next-hack/uSVC/images/32spritedemo.png

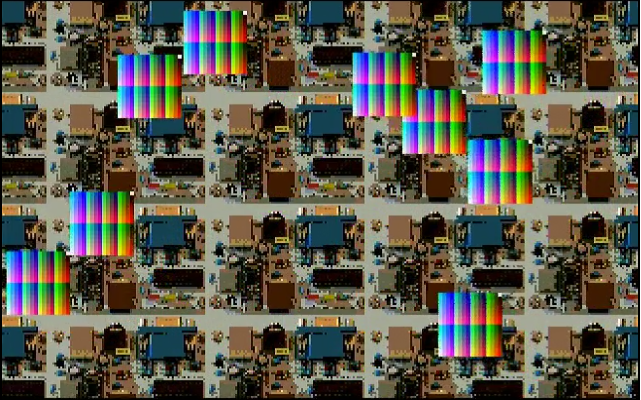
images/32spritedemo.png
