next-hack/uSVC/images/gameLoader.png

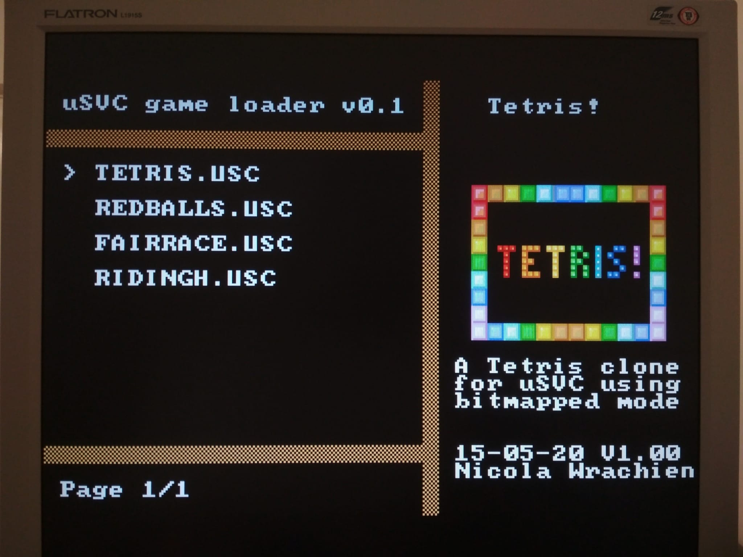
images/gameLoader.png
