next-hack/uSVC/images/redballs1.png

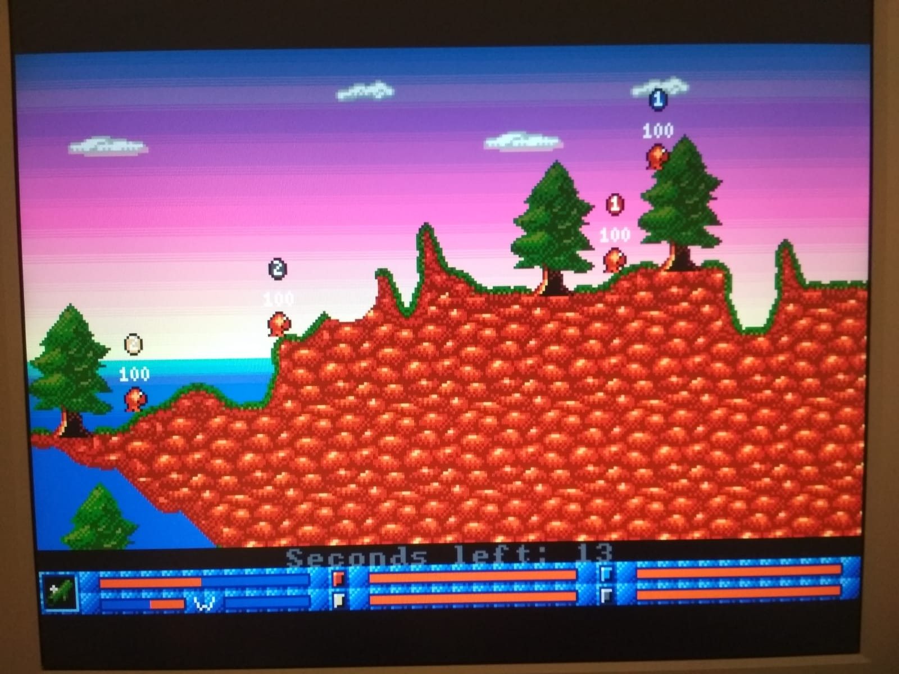
images/redballs1.png
