next-hack/uSVC/images/redballs2.png

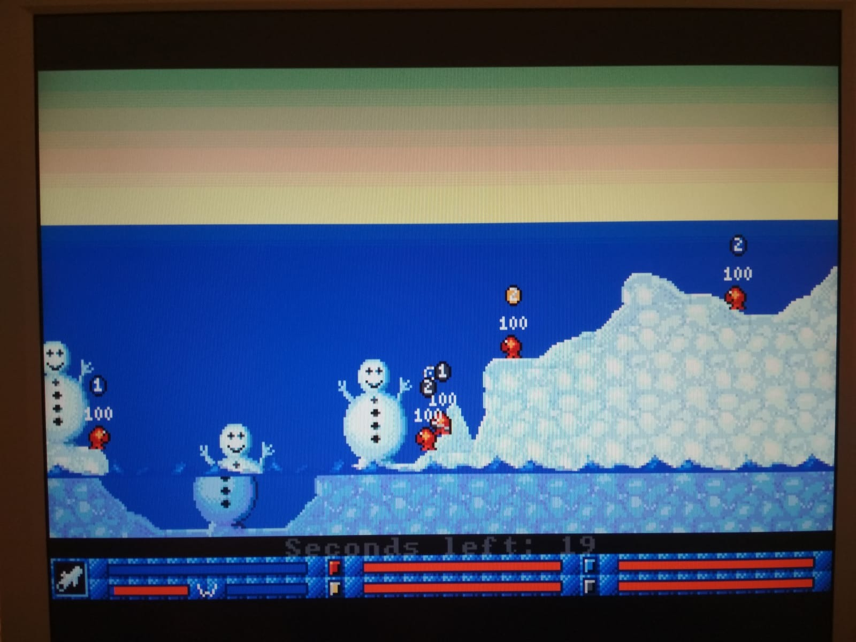
images/redballs2.png
