next-hack/uSVC/images/riding horse.png

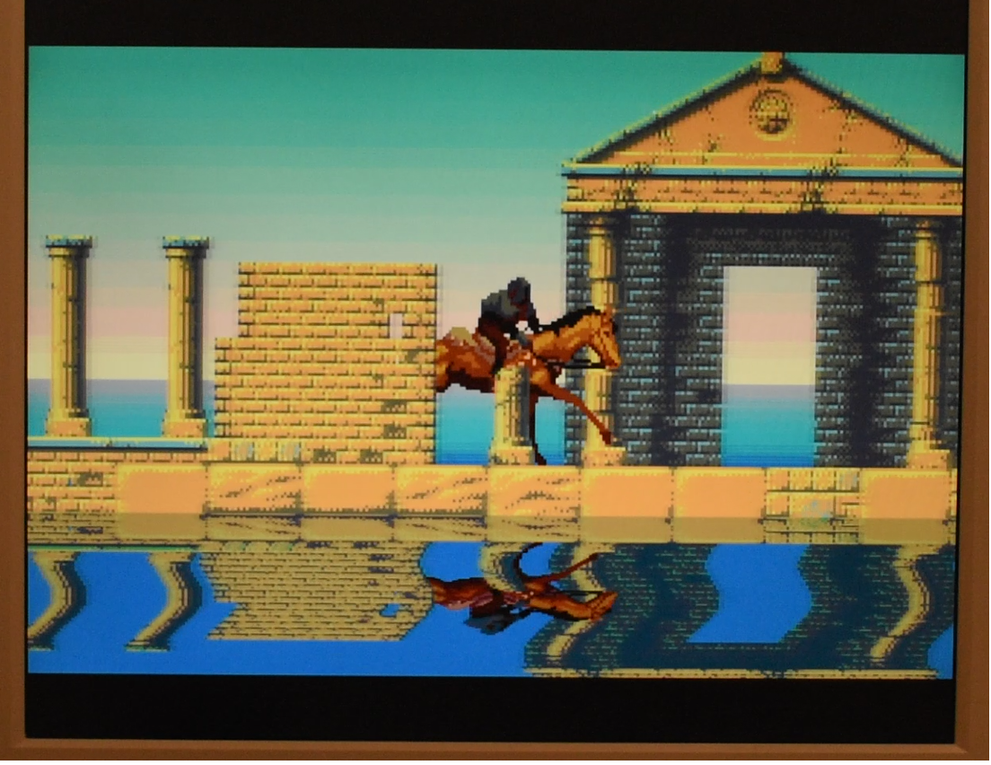
images/riding horse.png
