next-hack/uSVC/images/sprites8x8.png

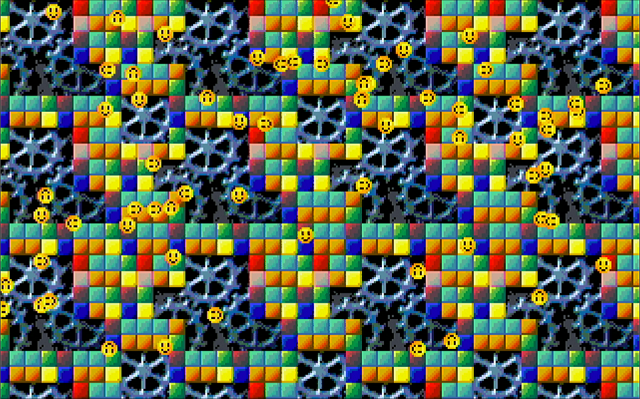
images/sprites8x8.png
