next-hack/uSVC/images/usvc connected.jpg

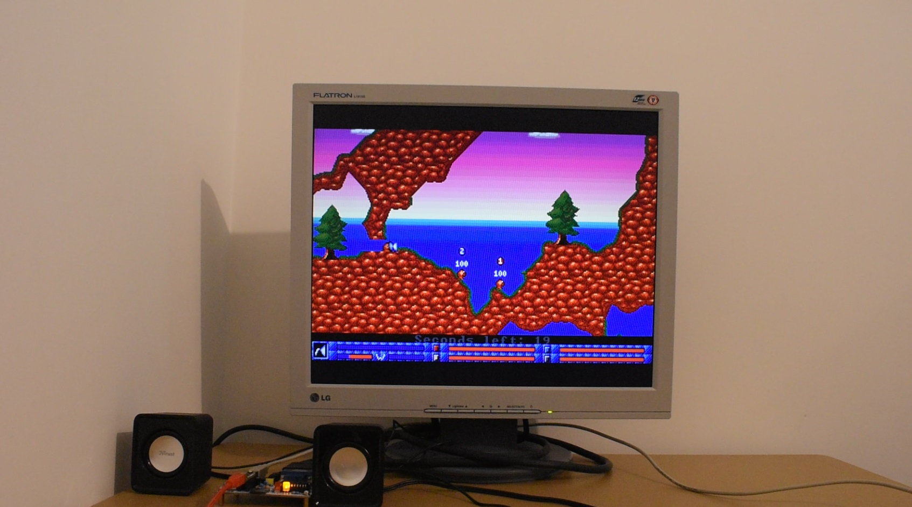
images/usvc connected.jpg
