next-hack/uSVC/images/usvc fits in your hand-red.jpg

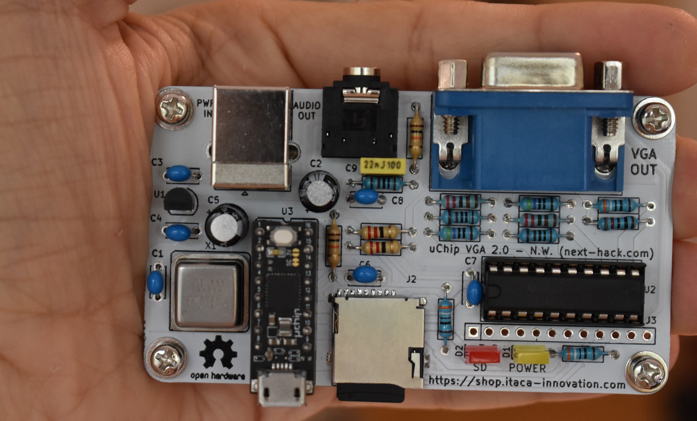
images/usvc fits in your hand-red.jpg
