next-hack/uSVC/images/usvcEditor.png

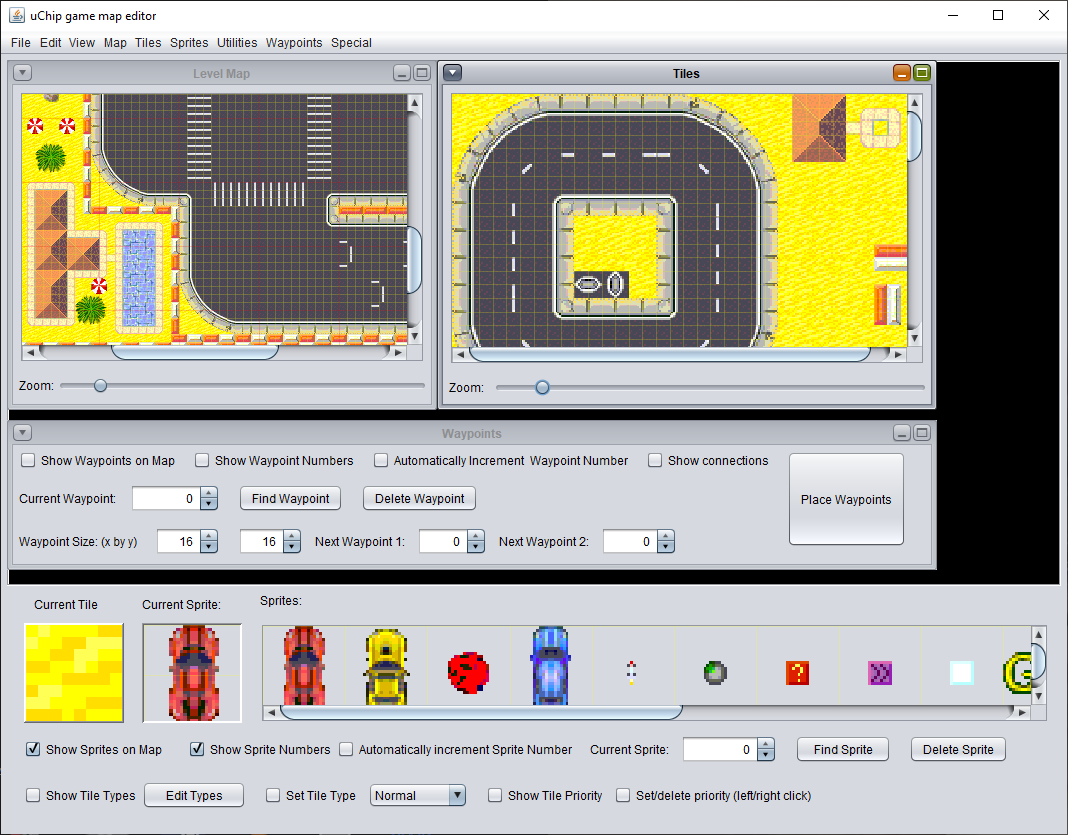
images/usvcEditor.png
