next-hack/uSVC/software/uSVC_GameLoader/soundData.c

/*
 *  RedBalls (not in the UrbanDictionary definintion!): 
 *  A clone of the popular Worms game, runnin on uChip Simple VGA Console
 *  a simple Cortex M0+ console with 32 kB of RAM!
 *
 *  Copyright 2019-2020 Nicola Wrachien (next-hack.com)
 *
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
 *  tl;dr 
 *  Do whatever you want, this program is free! Though we won't 
 *  reject donations https://next-hack.com/index.php/donate/ :) 
 *
 *
 * soundData.h/c: these files defines the actual PCM samples. 
 * I used  WAVToCode (Copyright (C) 2018-2020 C. J. Seymour)
 * to create the arrays. 
 */
#include "soundData.h" 
/**********************************************************************
* Written by WAVToCode
* Date:				Thu Apr 02 09:02:51 AM
* FileName:			ak47.c
* Interleaved:		N/A
* Signed:			Yes
* No. of channels:	1
* No. of samples:	1268
* Bits/Sample:		8
* Sps: 30k
**********************************************************************/

const char ak47_data[AK47_NUM_ELEMENTS] = {
	0,   0,   0,   0,   0,   0,   0,   0, /* 0-7 */
	0,   0,   0,   0,   0,   0,   0,   0, /* 8-15 */
	0,   0,   0,   0,   0,   0,   0,   0, /* 16-23 */
	0,   0,   0,   0,   0,   0,   0,   0, /* 24-31 */
	0,   0,   0,   0,   0,   0,   0,   0, /* 32-39 */
	0,   0,   0,   0,   0,   0,   0,   0, /* 40-47 */
	0,   0,   0,   0,   0,   0,   0,   0, /* 48-55 */
	0,   0,   0,   0,   0,   0,   0,   0, /* 56-63 */
	0,   0,   0,   0,   0,   0,   0,   0, /* 64-71 */
	-1,   0,  -2,  -6, -12,  16,  42,  33, /* 72-79 */
	28,  18,  17,  15,   2,  -6, -13, -17, /* 80-87 */
	-15, -14, -16, -14, -12, -11, -11, -11, /* 88-95 */
	-9,  -7,  -8,  -6,  -3,  -1,   0,   0, /* 96-103 */
	0,   1,  -1,  -2,   3,   2,   1,  -1, /* 104-111 */
	0,   2,  -1,   3,   0,   0,   2,   0, /* 112-119 */
	2,   0,   1,   1,   1,   0,  -1,   1, /* 120-127 */
	0,  -1,  -2,  -1,   0,   0,  -1,   1, /* 128-135 */
	1,   0,  -1,  -2,   1,   3,   0,  -3, /* 136-143 */
	-2,  -1,   0,   0,  -1,  -1,   0,  -1, /* 144-151 */
	-1,   0,  -1,  -1,   0,  -1,  -1,  -1, /* 152-159 */
	0,   0,   0,   0,  -1,  -1,   0,   0, /* 160-167 */
	0,  -1,  -1,   0,   0,   0,   0,  -1, /* 168-175 */
	0,   0,   0,   0,   0,   0,  -1,   0, /* 176-183 */
	-2,  -1,   0,   0,   0,  -1,  -1,   0, /* 184-191 */
	0,  -1,  -2,  -1,   0,  -1,   0,  -1, /* 192-199 */
	0,  -2,  -1,   0,  -1,   0,  -1,   0, /* 200-207 */
	-1,  -1,   0,   0,   1,  -1,  -1,   0, /* 208-215 */
	-1,  -1,  -1,   0,  -1,  -1,   0,   0, /* 216-223 */
	0,  -1,  -1,  -1,  -1,   0,  -1,  -1, /* 224-231 */
	-1,  -1,   0,  -1,  -1,  -1,  -1,  -1, /* 232-239 */
	0,   0,   0,  -1,  -1,  -1,   0,  -1, /* 240-247 */
	-1,  -1,  -1,   0,  -1,  -1,  -1,   0, /* 248-255 */
	-1,  -1,   0,   0,  -1,  -1,  -1,   0, /* 256-263 */
	0,   0,  -1,   0,  -1,  -1,  -1,  -1, /* 264-271 */
	0,  -1,   0,  -1,   0,  -1,   0,  -1, /* 272-279 */
	-1,  -2,  -1,   0,   0,  -2,  -1,  -1, /* 280-287 */
	0,   0,   0,  -1,  -1,   1,  -1,   0, /* 288-295 */
	-1,   0,  -2,   1,  -2,   2,  -3,   4, /* 296-303 */
	-4,   7, -28, -56, -62, -57,  35,  65, /* 304-311 */
	117, 127, 124,  63,  -4, -18, -53, -67, /* 312-319 */
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
	
