next-hack/uSVC/software/uSVC_GameLoader/usvc_kernel/defaultSounds.c

/*
*  Default UzeBox sounds, copyright Alec Bourque (Belogic Software, UzeBox project).
*  
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
*  You should have received a copy of the GNU General Public License
*  along with this program.  If not, see <http://www.gnu.org/licenses/>. 
*/
#include <stdint.h> 
#include "defaultSounds.h"
#if INCLUDE_DEFAULT_WAVES
const int8_t sineWave[] =
{
	0x00,0x03,0x06,0x09,0x0C,0x10,0x13,0x16,0x19,0x1C,0x1F,0x22,0x25,0x28,0x2B,0x2E,
	0x31,0x33,0x36,0x39,0x3C,0x3F,0x41,0x44,0x47,0x49,0x4C,0x4E,0x51,0x53,0x55,0x58,
	0x5A,0x5C,0x5E,0x60,0x62,0x64,0x66,0x68,0x6A,0x6B,0x6D,0x6F,0x70,0x71,0x73,0x74,
	0x75,0x76,0x78,0x79,0x7A,0x7A,0x7B,0x7C,0x7D,0x7D,0x7E,0x7E,0x7E,0x7F,0x7F,0x7F,
	0x7F,0x7F,0x7F,0x7F,0x7E,0x7E,0x7E,0x7D,0x7D,0x7C,0x7B,0x7A,0x7A,0x79,0x78,0x76,
	0x75,0x74,0x73,0x71,0x70,0x6F,0x6D,0x6B,0x6A,0x68,0x66,0x64,0x62,0x60,0x5E,0x5C,
	0x5A,0x58,0x55,0x53,0x51,0x4E,0x4C,0x49,0x47,0x44,0x41,0x3F,0x3C,0x39,0x36,0x33,
	0x31,0x2E,0x2B,0x28,0x25,0x22,0x1F,0x1C,0x19,0x16,0x13,0x10,0x0C,0x09,0x06,0x03,
	0x00,0xFD,0xFA,0xF7,0xF4,0xF0,0xED,0xEA,0xE7,0xE4,0xE1,0xDE,0xDB,0xD8,0xD5,0xD2,
	0xCF,0xCD,0xCA,0xC7,0xC4,0xC1,0xBF,0xBC,0xB9,0xB7,0xB4,0xB2,0xAF,0xAD,0xAB,0xA8,
	0xA6,0xA4,0xA2,0xA0,0x9E,0x9C,0x9A,0x98,0x96,0x95,0x93,0x91,0x90,0x8F,0x8D,0x8C,
	0x8B,0x8A,0x88,0x87,0x86,0x86,0x85,0x84,0x83,0x83,0x82,0x82,0x82,0x81,0x81,0x81,
	0x81,0x81,0x81,0x81,0x82,0x82,0x82,0x83,0x83,0x84,0x85,0x86,0x86,0x87,0x88,0x8A,
	0x8B,0x8C,0x8D,0x8F,0x90,0x91,0x93,0x95,0x96,0x98,0x9A,0x9C,0x9E,0xA0,0xA2,0xA4,
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
	,0x80,0x80,0x80,0x80,0x80,0x80,0x80,0x80,0x80,0x80,0x80,0x80,0x80,0x80,0x80,0x80
	,0x80,0x80,0x80,0x80,0x80,0x80,0x80,0x80,0x80,0x80,0x80,0x80,0x80,0x80,0x80,0x80
	,0x80,0x80,0x80,0x80,0x80,0x87,0x91,0x9d,0xac,0xc4,0xcb,0xd4,0xdd,0xf2,0xfa,0xfa	
};

#endif
