next-hack/uSVC/software/uSVC_GameLoader/usvc_kernel/stepTable.c

/*
*  uChip Simple VGA Console Kernel, a minimalistic console with VGA and USB support using uChip!
*
*  Copyright 2019-2020 Nicola Wrachien (next-hack.com)
*
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
*  tl;dr
*  Do whatever you want, this program is free! Though we won't
*  reject donations https://next-hack.com/index.php/donate/ :)
*
*  stepTable.c. Since the sampling frequency is fixed at 30kHz, and the
*  default sounds have 256 samples, for each note we need an increment
*  for decimation/integration.
*/
#include <stdint.h> 
const uint16_t stepTable[128] =
{
	0x0012, // Note 0 (C-1), frequency 8.175799, Step 0.070313
	0x0013, // Note 1 (C#-1), frequency 8.661957, Step 0.074219
	0x0014, // Note 2 (D-1), frequency 9.177024, Step 0.078125
	0x0015, // Note 3 (D#-1), frequency 9.722718, Step 0.082031
	0x0017, // Note 4 (E-1), frequency 10.300861, Step 0.089844
	0x0018, // Note 5 (F-1), frequency 10.913382, Step 0.093750
	0x0019, // Note 6 (F#-1), frequency 11.562326, Step 0.097656
	0x001B, // Note 7 (G-1), frequency 12.249857, Step 0.105469
	0x001C, // Note 8 (G#-1), frequency 12.978272, Step 0.109375
	0x001E, // Note 9 (A-1), frequency 13.750000, Step 0.117188
	0x0020, // Note 10 (A#-1), frequency 14.567618, Step 0.125000
	0x0022, // Note 11 (B-1), frequency 15.433853, Step 0.132813
	0x0024, // Note 12 (C-2), frequency 16.351598, Step 0.140625
	0x0026, // Note 13 (C#-2), frequency 17.323914, Step 0.148438
	0x0028, // Note 14 (D-2), frequency 18.354048, Step 0.156250
	0x002A, // Note 15 (D#-2), frequency 19.445436, Step 0.164063
	0x002D, // Note 16 (E-2), frequency 20.601722, Step 0.175781
	0x0030, // Note 17 (F-2), frequency 21.826764, Step 0.187500
	0x0033, // Note 18 (F#-2), frequency 23.124651, Step 0.199219
	0x0036, // Note 19 (G-2), frequency 24.499715, Step 0.210938
	0x0039, // Note 20 (G#-2), frequency 25.956544, Step 0.222656
	0x003C, // Note 21 (A-2), frequency 27.500000, Step 0.234375
	0x0040, // Note 22 (A#-2), frequency 29.135235, Step 0.250000
	0x0043, // Note 23 (B-2), frequency 30.867706, Step 0.261719
	0x0047, // Note 24 (C-3), frequency 32.703196, Step 0.277344
	0x004C, // Note 25 (C#-3), frequency 34.647829, Step 0.296875
	0x0050, // Note 26 (D-3), frequency 36.708096, Step 0.312500
	0x0055, // Note 27 (D#-3), frequency 38.890873, Step 0.332031
	0x005A, // Note 28 (E-3), frequency 41.203445, Step 0.351563
	0x005F, // Note 29 (F-3), frequency 43.653529, Step 0.371094
	0x0065, // Note 30 (F#-3), frequency 46.249303, Step 0.394531
	0x006B, // Note 31 (G-3), frequency 48.999429, Step 0.417969
	0x0071, // Note 32 (G#-3), frequency 51.913087, Step 0.441406
	0x0078, // Note 33 (A-3), frequency 55.000000, Step 0.468750
	0x007F, // Note 34 (A#-3), frequency 58.270470, Step 0.496094
	0x0087, // Note 35 (B-3), frequency 61.735413, Step 0.527344
	0x008F, // Note 36 (C-4), frequency 65.406391, Step 0.558594
	0x0097, // Note 37 (C#-4), frequency 69.295658, Step 0.589844
	0x00A0, // Note 38 (D-4), frequency 73.416192, Step 0.625000
	0x00AA, // Note 39 (D#-4), frequency 77.781746, Step 0.664063
	0x00B4, // Note 40 (E-4), frequency 82.406889, Step 0.703125
	0x00BF, // Note 41 (F-4), frequency 87.307058, Step 0.746094
	0x00CA, // Note 42 (F#-4), frequency 92.498606, Step 0.789063
	0x00D6, // Note 43 (G-4), frequency 97.998859, Step 0.835938
	0x00E3, // Note 44 (G#-4), frequency 103.826174, Step 0.886719
	0x00F0, // Note 45 (A-4), frequency 110.000000, Step 0.937500
	0x00FF, // Note 46 (A#-4), frequency 116.540940, Step 0.996094
	0x010E, // Note 47 (B-4), frequency 123.470825, Step 1.054688
	0x011E, // Note 48 (C-5), frequency 130.812783, Step 1.117188
	0x012F, // Note 49 (C#-5), frequency 138.591315, Step 1.183594
	0x0141, // Note 50 (D-5), frequency 146.832384, Step 1.253906
	0x0154, // Note 51 (D#-5), frequency 155.563492, Step 1.328125
	0x0168, // Note 52 (E-5), frequency 164.813778, Step 1.406250
	0x017D, // Note 53 (F-5), frequency 174.614116, Step 1.488281
	0x0194, // Note 54 (F#-5), frequency 184.997211, Step 1.578125
	0x01AC, // Note 55 (G-5), frequency 195.997718, Step 1.671875
	0x01C6, // Note 56 (G#-5), frequency 207.652349, Step 1.773438
	0x01E1, // Note 57 (A-5), frequency 220.000000, Step 1.878906
	0x01FD, // Note 58 (A#-5), frequency 233.081881, Step 1.988281
	0x021B, // Note 59 (B-5), frequency 246.941651, Step 2.105469
	0x023C, // Note 60 (C-6), frequency 261.625565, Step 2.234375
	0x025E, // Note 61 (C#-6), frequency 277.182631, Step 2.367188
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
	0x5A03, // Note 124 (E-11), frequency 10548.081821, Step 90.011719
	0x5F5D, // Note 125 (F-11), frequency 11175.303406, Step 95.363281
	0x6508, // Note 126 (F#-11), frequency 11839.821527, Step 101.031250
	0x6B0A // Note 127 (G-11), frequency 12543.853951, Step 107.039063
};
