next-hack/uSVC/software/uSVC_GameLoader/logoTiles.c

/*	USVC Game Loader and libraries
*
 *  Copyright 2019-2020 Nicola Wrachien (next-hack.com)
 *
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
 *  tl;dr 
 *  Do whatever you want, this program is free! Though we won't 
 *  reject donations https://next-hack.com/index.php/donate/ :) 
 *
 */
#include "logoTiles.h"
#include "usvc_kernel/vgaConstants.h"
const uint8_t tilePalette[] = 
{0x00 , 0x56, 0x97, 0xD7, 
0x00 , COLOR_TORGB332(7, 4, 0), COLOR_TORGB332(7, 7, 0), COLOR_TORGB332(7, 7, 2),
0x00 , COLOR_TORGB332(7, 5, 1), COLOR_TORGB332(7, 7, 1), COLOR_TORGB332(7, 7, 3),
0x00 , COLOR_TORGB332(7, 6, 2), COLOR_TORGB332(7, 7, 2), COLOR_TORGB332(7, 7, 3),
0x00 , COLOR_TORGB332(7, 6, 3), COLOR_TORGB332(7, 7, 3), COLOR_TORGB332(7, 7, 3),
0x00 , COLOR_TORGB332(7, 6, 2), COLOR_TORGB332(7, 7, 2), COLOR_TORGB332(7, 7, 3),
0x00 , COLOR_TORGB332(7, 5, 1), COLOR_TORGB332(7, 7, 1), COLOR_TORGB332(7, 7, 3),
0x00 , COLOR_TORGB332(7, 4, 0), COLOR_TORGB332(7, 7, 0), COLOR_TORGB332(7, 7, 2),
0x00, COLOR_TORGB332(6, 3, 0), COLOR_TORGB332(7, 5, 0), COLOR_TORGB332(7, 7, 0),
0x00, COLOR_TORGB332(4, 2, 0), COLOR_TORGB332(5, 3, 0), COLOR_TORGB332(5, 4, 0),
0x00, COLOR_TORGB332(2, 1, 0), COLOR_TORGB332(3, 2, 0), COLOR_TORGB332(3, 3, 0),
0x00, COLOR_TORGB332(1, 0, 0), COLOR_TORGB332(2, 1, 0), COLOR_TORGB332(2, 2, 0),
0x00, COLOR_TORGB332(0, 0, 0), COLOR_TORGB332(1, 0, 0), COLOR_TORGB332(1, 1, 0),
0x00, 0, 0, 0,
}; // the second part is the highlighted one

const uint8_t tileData[MAXTILEINDEX][TILESIZEX * TILESIZEY / 4 ] =
{
// 	{  first tile is black. We wont' save it!
// 		0x00, 0x00, 0x00, 0x00, 0x00, 0x00, 0x00, 0x00, 0x00, 0x00, 0x00, 0x00, 0x00, 0x00, 0x00, 0x00
// 	},
	{
		0x00, 0x40, 0x00, 0x90, 0x00, 0xE4, 0x00, 0xF9, 0x40, 0xFE, 0x90, 0xFF, 0xE4, 0xFF, 0xF9, 0xFF
	},
	{
		0x55, 0x55, 0xAA, 0xAA, 0xFF, 0xFF, 0xFF, 0xFF, 0xFF, 0xFF, 0xFF, 0xFF, 0xFF, 0xFF, 0xFF, 0xFF
	},
	{
		0x01, 0x00, 0x06, 0x00, 0x1B, 0x00, 0x6F, 0x00, 0xBF, 0x01, 0xFF, 0x06, 0xFF, 0x1B, 0xFF, 0x6F
	},
	{
		0xFF, 0xFF, 0xFF, 0xFF, 0xFF, 0xFF, 0xFF, 0xFF, 0xFF, 0xFF, 0xFF, 0xFF, 0xFF, 0xFF, 0xFF, 0xBF
	},
	{
		0xFF, 0xFF, 0xFF, 0xFF, 0xFF, 0xFF, 0xFF, 0xFF, 0xFF, 0xFF, 0xFF, 0xFF, 0xFF, 0xFF, 0xFE, 0xFF
	},
	{
		0xF9, 0xFF, 0xF9, 0xFF, 0xF9, 0xFF, 0xF9, 0xFF, 0xF9, 0xFF, 0xF9, 0xFF, 0xF9, 0xFF, 0xF9, 0xFF
	},
	{
		0xFF, 0xFF, 0xFF, 0xFF, 0xFF, 0xFF, 0xFF, 0xFF, 0xFF, 0xFF, 0xFF, 0xFF, 0xFF, 0xFF, 0xFF, 0xFF
	},
	{
		0xFF, 0x6F, 0xFF, 0x6F, 0xFF, 0x6F, 0xFF, 0x6F, 0xFF, 0x6F, 0xFF, 0x6F, 0xFF, 0x6F, 0xFF, 0x6F
	},
	{
		0xFF, 0xBF, 0xFF, 0xFF, 0xFF, 0xFF, 0xFF, 0xFF, 0xFF, 0xFF, 0xFF, 0xFF, 0xFF, 0xFF, 0xFF, 0xFF
	},
	{
		0xFE, 0xFF, 0xFF, 0xFF, 0xFF, 0xFF, 0xFF, 0xFF, 0xFF, 0xFF, 0xFF, 0xFF, 0xFF, 0xFF, 0xFF, 0xFF
	},
	{
		0xF9, 0xFF, 0xE4, 0xFF, 0x90, 0xFF, 0x40, 0xFE, 0x00, 0xF9, 0x00, 0xE4, 0x00, 0x90, 0x00, 0x40
	},
	{
		0xFF, 0xFF, 0xFF, 0xFF, 0xFF, 0xFF, 0xFF, 0xFF, 0xFF, 0xFF, 0xFF, 0xFF, 0xAA, 0xAA, 0x55, 0x55
	},
	{
		0xFF, 0x6F, 0xFF, 0x1B, 0xFF, 0x06, 0xBF, 0x01, 0x6F, 0x00, 0x1B, 0x00, 0x06, 0x00, 0x01, 0x00
	}
};
