next-hack/uSVC/software/uSVC_GameLoader/usvcLogoMap.c

/*	USVC Game Loader and libraries
*
 *  Copyright 2019-2020 Nicola Wrachien (next-hack.com)
 *
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
 *  tl;dr 
 *  Do whatever you want, this program is free! Though we won't 
 *  reject donations https://next-hack.com/index.php/donate/ :) 
 *
 */
#include "usvcLogoMap.h"
#define NIBBLES2B(a,b) (a | (b << 4))
#define ROWOFNIBBLES2BYTES(a0, a1, a2, a3, a4, a5, a6, a7)  NIBBLES2B(a0,a1),NIBBLES2B(a2,a3),NIBBLES2B(a4,a5),NIBBLES2B(a6,a7)
const uint8_t logoMap[MAPSIZEY_LOGO * MAPSIZEX_LOGO/2] =
{
	ROWOFNIBBLES2BYTES(0x0000, 0x0000, 0x0000, 0x0000, 0x0000, 0x0000, 0x0000, 0x0000),
	ROWOFNIBBLES2BYTES(0x0000, 0x0001, 0x0002, 0x0002, 0x0002, 0x0002, 0x0002, 0x0003),
	ROWOFNIBBLES2BYTES(0x0000, 0x0001, 0x0003, 0x0000, 0x0000, 0x0000, 0x0000, 0x0001),
	ROWOFNIBBLES2BYTES(0x0003, 0x0000, 0x0000, 0x0001, 0x0002, 0x0002, 0x0002, 0x0002),
	ROWOFNIBBLES2BYTES(0x0002, 0x0003, 0x0000, 0x0000, 0x0000, 0x0000, 0x0000, 0x0000),
	ROWOFNIBBLES2BYTES(0x0000, 0x0000, 0x0001, 0x000A, 0x0004, 0x000C, 0x000C, 0x000C),
	ROWOFNIBBLES2BYTES(0x000C, 0x000D, 0x0000, 0x0006, 0x0008, 0x0000, 0x0000, 0x0000),
	ROWOFNIBBLES2BYTES(0x0000, 0x0006, 0x0008, 0x0000, 0x0001, 0x000A, 0x0004, 0x000C),
	ROWOFNIBBLES2BYTES(0x000C, 0x000C, 0x000C, 0x000D, 0x0000, 0x0000, 0x0000, 0x0000),
	ROWOFNIBBLES2BYTES(0x0000, 0x0000, 0x0000, 0x0000, 0x0006, 0x0004, 0x000D, 0x0000),
	ROWOFNIBBLES2BYTES(0x0000, 0x0000, 0x0000, 0x0000, 0x0000, 0x0006, 0x0008, 0x0000),
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
	ROWOFNIBBLES2BYTES(0x0000, 0x0000, 0x0000, 0x0000, 0x0000, 0x0000, 0x0000, 0x0000),
	ROWOFNIBBLES2BYTES(0x0000, 0x0000, 0x0000, 0x0000, 0x0000, 0x0000, 0x0000, 0x0000),
	ROWOFNIBBLES2BYTES(0x0000, 0x0000, 0x0000, 0x0000, 0x0000, 0x0000, 0x0000, 0x0000),
	NIBBLES2B(0x0000, 0x0000)
};
