next-hack/uSVC/software/uSVC_GameLoader/usvc_kernel/rand.c

/*-
 * Copyright (c) 1990, 1993
 *	The Regents of the University of California.  All rights reserved.
 *
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
 * Posix rand_r function added May 1999 by Wes Peters <wes@softweyr.com>.
 */

#include <stdlib.h>

static unsigned long next = 1;
static int do_rand(unsigned long* ctx)
{
#ifdef USE_WEAK_SEEDING
	/*
	 * Historic implementation compatibility.
	 * The random sequences do not vary much with the seed,
	 * even with overflowing.
	 */
	return ((*ctx = *ctx * 1103515245 + 12345) % ((unsigned long)RAND_MAX + 1));
#else /* !USE_WEAK_SEEDING */
	/*
	 * Compute x = (7^5 * x) mod (2^31 - 1)
	 * without overflowing 31 bits:
	 *      (2^31 - 1) = 127773 * (7^5) + 2836
	 * From "Random number generators: good ones are hard to find",
	 * Park and Miller, Communications of the ACM, vol. 31, no. 10,
	 * October 1988, p. 1195.
	 */
	long hi;
	long lo;
	long x;

	/* Can't be initialized with 0, so use another value. */
	if(*ctx == 0)
	{
		*ctx = 123459876UL;
	}

	hi = (long)(*ctx / 127773L);
	lo = (long)(*ctx % 127773L);
	x = 16807 * lo - 2836 * hi;

	if(x < 0)
	{
		x += 0x7fffffff;
	}

	return (int)((*ctx = (unsigned long)x) % ((unsigned long)RAND_MAX + 1));
#endif /* !USE_WEAK_SEEDING */
}

__attribute__((weak)) int rand_r(unsigned int* ctx)
{
	unsigned long val = (unsigned long)*ctx;
	int r = do_rand(&val);

	*ctx = (unsigned int)val;
	return (r);
}

__attribute__((weak)) int rand()
{
	return (do_rand(&next));
}

__attribute__((weak)) void srand(unsigned seed)
{
	next = seed;
}
