next-hack/uSVC/software/uSVC_Demos_And_Tutorials/uSVC_RidingHorseDemo/main.c

/*
 *  Riding Horse demo. 
 *  Copyright 2019-2020 Nicola Wrachien (next-hack.com)
 *  A simple demo to show the most exciting features of the TILE_MODE22
 *  1) High res per line x scroll to create water deformation
 *  2) High res row remapping to create water mirror
 *  3) High res Palette change for water color distortion
 *  4) Per line color change to create sky shades
 *  5) Tile prioirity
 *  6) Sprite prioirity
 *
 *  Credits: the graphics of this game (namely the riding horse, the clouds and the tiles) have been taken from opengameart.org, and recoloured to better
 *  fit a 16-color palette.
 *  In particular:
 *  Original assassin character riding a horse: Author Stagnation. Original URL: https://opengameart.org/content/assassin-character-on-horse (License GPL3)
 *  Original classical ruin tiles: Author surt. Original URL: https://opengameart.org/content/classical-ruin-tiles (License: CC0 - public domain)
 *  The graphics is copyright of their respective authors. 
 *
 *  Note: this demo is not optimized for game, just to show some of the most important features all at once. 
 *  Better optimization (especially by using rom vectors) can be achieved fo save tons of RAM!
 *
 *  Warning: the code needs a clean-up, and there might be some unused additional files and functions.
 *
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
 *  tl;dr 
 *  Do whatever you want, this program is free! Though we won't 
 *  reject donations https://next-hack.com/index.php/donate/ :) 
 *
 */
#include "main.h"
#define NO_USB 0			// 1 for testing
#if RAMTILES > MAX_TILES 
	#error you must adjust the number of MAX_TILES in VGA.h
#endif
#define WATER_START 200
#define SPRITE_IS_MOVED_BY_USB_INPUT 0
#define CHECKPOINT_PERIOD 16
#define CHECKPOINT_PERIOD_LOG2 4
#define CHECKPOINT_PALETTES 2
#define CHANGED_PALETTE_ENTRIES 16
#include <stdlib.h>
// Clouds. Used the same algorithm of RedBalls
#define CLOUD_PATTERN_WIDTH 360
#define NUMBER_OF_CLOUDS 1
const uint16_t cloudY[] = {64, 64};
const uint16_t cloudX[] = {200, 600};
const uint16_t cloudFrames[] = {CLOUD1_CLOUD_FRAMEINDEX, CLOUD3_CLOUD_FRAMEINDEX, CLOUD2_CLOUD_FRAMEINDEX};
int32_t cloudPatternX = 0;
// Fixed section: disabled.
#if USE_FIXED_SECTION != NO_FIXED_SECTION
uint32_t fixedSectionTiles[MAX_FIXED_SECTION_TILES][16] __attribute__ ((aligned (4)));
uint8_t fixedSectionMap[FIXED_SECTION_MAPSIZEX * FIXED_SECTION_MAPSIZEY]  __attribute__ ((aligned (4)));
#endif
uint8_t currentLevel = 0;
static uint16_t g_frame = 0;	
#if PER_TILE_X_SCROLL	
	uint8_t xScrollTileTable[VRAMY];
#endif
// Row remapTable could be probably made const with some tricks., saving a lot of ram.
#if USE_ROW_REMAPPING
	uint8_t rowRemapTable[416];
#endif
// Similarly, xScrollTable coul be made in ROM
#if PER_LINE_X_SCROLL
	uint8_t xScrollTable[416];
#endif
// Water displacement array. Precalculated of course.
#define MAX_WATER_INDEX (7*8*2)
const uint8_t waterDisplacementArray[57 * MAX_WATER_INDEX] =
{
	0, 1, 1, 1, 0, 0, 0, 0, 0, 0, 0, 0, 0, 0, 0, 1, 1, 2, 2, 2, 3, 3, 4, 4, 4, 4, 4, 4, 4, 4, 4, 4, 4, 4, 3, 3, 3, 2, 2, 2, 1, 1, 1, 0, 0, 0, 0, 0, 0, 0, 0, 0, 0, 0, 0, 0, 1, 1, 2, 2, 2, 3, 4, 4, 5, 5, 6, 6, 7, 8, 8, 9, 9, 10, 10, 11, 11, 11, 12, 12, 12, 12, 12, 12, 12, 12, 12, 12, 12, 12, 12, 11, 11, 11, 10, 10, 9, 9, 8, 8, 7, 7, 6, 6, 5, 4, 4, 3, 3, 2, 2, 2,
	0, 1, 1, 1, 0, 0, 0, 0, 0, 0, 0, 0, 0, 0, 0, 1, 1, 1, 2, 2, 3, 3, 3, 4, 4, 4, 4, 4, 4, 4, 4, 4, 4, 4, 4, 3, 3, 3, 2, 2, 2, 1, 1, 1, 0, 0, 0, 0, 0, 0, 0, 0, 0, 0, 0, 0, 0, 1, 1, 2, 2, 2, 3, 4, 4, 5, 5, 6, 6, 7, 8, 8, 9, 9, 10, 10, 11, 11, 11, 12, 12, 12, 12, 12, 13, 13, 13, 13, 12, 12, 12, 12, 12, 11, 11, 10, 10, 10, 9, 9, 8, 8, 7, 6, 6, 5, 5, 4, 4, 3, 3, 2,
	0, 1, 1, 1, 1, 0, 0, 0, 0, 0, 0, 0, 0, 0, 0, 0, 1, 1, 2, 2, 2, 3, 3, 4, 4, 4, 4, 4, 5, 5, 5, 4, 4, 4, 4, 4, 3, 3, 3, 2, 2, 2, 1, 1, 1, 0, 0, 0, 0, 0, 0, 0, 0, 0, 0, 0, 0, 0, 1, 1, 2, 2, 2, 3, 4, 4, 5, 5, 6, 6, 7, 8, 8, 9, 9, 10, 10, 11, 11, 11, 12, 12, 12, 12, 13, 13, 13, 13, 13, 13, 12, 12, 12, 12, 11, 11, 11, 10, 10, 9, 9, 8, 8, 7, 7, 6, 6, 5, 4, 4, 3, 3,
	0, 1, 1, 1, 1, 0, 0, 0, 0, 0, 0, 0, 0, 0, 0, 0, 1, 1, 1, 2, 2, 3, 3, 3, 4, 4, 4, 4, 5, 5, 5, 5, 5, 4, 4, 4, 4, 3, 3, 3, 2, 2, 2, 1, 1, 1, 0, 0, 0, 0, 0, 0, 0, 0, 0, 0, 0, 0, 0, 1, 1, 2, 2, 2, 3, 4, 4, 5, 5, 6, 6, 7, 8, 8, 9, 9, 10, 10, 11, 11, 12, 12, 12, 12, 13, 13, 13, 13, 13, 13, 13, 13, 13, 12, 12, 12, 11, 11, 11, 10, 10, 9, 9, 8, 8, 7, 6, 6, 5, 5, 4, 4,
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
	0, 0, 0, 0, 0, 0, 1, 1, 2, 2, 2, 2, 2, 2, 2, 2, 2, 2, 1, 1, 1, 1, 0, 0, 0, 0, 0, 0, 0, 0, 0, 0, 0, 0, 1, 1, 1, 2, 2, 3, 3, 4, 4, 5, 5, 6, 6, 7, 7, 7, 8, 8, 8, 8, 8, 8, 8, 8, 8, 8, 8, 8, 7, 7, 7, 6, 6, 5, 5, 4, 4, 4, 3, 3, 2, 2, 1, 1, 1, 0, 0, 0, 0, 0, 0, 0, 0, 0, 0, 0, 0, 0, 1, 1, 1, 2, 2, 3, 3, 4, 4, 5, 6, 6, 7, 7, 8, 9, 9, 10, 10, 11,
	0, 0, 0, 0, 0, 0, 1, 1, 1, 2, 2, 2, 2, 2, 2, 2, 2, 2, 2, 1, 1, 1, 0, 0, 0, 0, 0, 0, 0, 0, 0, 0, 0, 0, 0, 1, 1, 2, 2, 2, 3, 3, 4, 4, 5, 5, 6, 6, 7, 7, 7, 8, 8, 8, 8, 8, 8, 8, 8, 8, 8, 8, 8, 7, 7, 7, 6, 6, 6, 5, 5, 4, 4, 3, 3, 2, 2, 2, 1, 1, 1, 0, 0, 0, 0, 0, 0, 0, 0, 0, 0, 0, 0, 0, 1, 1, 2, 2, 2, 3, 4, 4, 5, 5, 6, 7, 7, 8, 8, 9, 10, 10,
	0, 0, 0, 0, 0, 0, 1, 1, 1, 2, 2, 2, 2, 2, 2, 2, 2, 2, 2, 2, 1, 1, 1, 0, 0, 0, 0, 0, 0, 0, 0, 0, 0, 0, 0, 1, 1, 1, 2, 2, 3, 3, 4, 4, 5, 5, 6, 6, 7, 7, 7, 8, 8, 8, 8, 8, 9, 9, 9, 9, 8, 8, 8, 8, 8, 7, 7, 7, 6, 6, 5, 5, 4, 4, 3, 3, 3, 2, 2, 1, 1, 1, 0, 0, 0, 0, 0, 0, 0, 0, 0, 0, 0, 0, 0, 1, 1, 1, 2, 2, 3, 3, 4, 5, 5, 6, 6, 7, 8, 8, 9, 9,
	0, 0, 0, 0, 0, 0, 0, 1, 1, 2, 2, 2, 2, 2, 2, 2, 2, 2, 2, 2, 1, 1, 1, 1, 0, 0, 0, 0, 0, 0, 0, 0, 0, 0, 0, 0, 1, 1, 1, 2, 2, 3, 3, 4, 4, 5, 5, 6, 6, 7, 7, 7, 8, 8, 8, 8, 9, 9, 9, 9, 9, 9, 8, 8, 8, 8, 7, 7, 7, 6, 6, 5, 5, 4, 4, 4, 3, 3, 2, 2, 1, 1, 1, 0, 0, 0, 0, 0, 0, 0, 0, 0, 0, 0, 0, 0, 1, 1, 1, 2, 2, 3, 3, 4, 4, 5, 5, 6, 7, 7, 8, 8,
	0, 0, 0, 0, 0, 0, 0, 1, 1, 2, 2, 2, 2, 2, 3, 3, 2, 2, 2, 2, 2, 1, 1, 1, 1, 0, 0, 0, 0, 0, 0, 0, 0, 0, 0, 0, 0, 1, 1, 1, 2, 2, 3, 3, 4, 4, 5, 5, 6, 6, 7, 7, 8, 8, 8, 8, 9, 9, 9, 9, 9, 9, 9, 9, 8, 8, 8, 8, 7, 7, 6, 6, 6, 5, 5, 4, 4, 3, 3, 2, 2, 2, 1, 1, 1, 0, 0, 0, 0, 0, 0, 0, 0, 0, 0, 0, 0, 0, 1, 1, 2, 2, 2, 3, 4, 4, 5, 5, 6, 6, 7, 8,
	1, 0, 0, 0, 0, 0, 0, 1, 1, 1, 2, 2, 2, 2, 3, 3, 3, 2, 2, 2, 2, 2, 1, 1, 1, 0, 0, 0, 0, 0, 0, 0, 0, 0, 0, 0, 0, 0, 1, 1, 2, 2, 2, 3, 3, 4, 4, 5, 5, 6, 6, 7, 7, 8, 8, 8, 9, 9, 9, 9, 9, 9, 9, 9, 9, 9, 8, 8, 8, 7, 7, 7, 6, 6, 5, 5, 4, 4, 3, 3, 3, 2, 2, 1, 1, 1, 0, 0, 0, 0, 0, 0, 0, 0, 0, 0, 0, 0, 0, 1, 1, 1, 2, 2, 3, 3, 4, 4, 5, 6, 6, 7,
	1, 0, 0, 0, 0, 0, 0, 1, 1, 1, 2, 2, 2, 2, 3, 3, 3, 3, 3, 2, 2, 2, 2, 1, 1, 1, 0, 0, 0, 0, 0, 0, 0, 0, 0, 0, 0, 0, 0, 1, 1, 2, 2, 3, 3, 4, 4, 5, 5, 6, 6, 7, 7, 7, 8, 8, 8, 9, 9, 9, 9, 9, 9, 9, 9, 9, 9, 9, 8, 8, 8, 7, 7, 6, 6, 5, 5, 5, 4, 4, 3, 3, 2, 2, 1, 1, 1, 0, 0, 0, 0, 0, 0, 0, 0, 0, 0, 0, 0, 0, 1, 1, 1, 2, 2, 3, 3, 4, 4, 5, 5, 6,
	1, 0, 0, 0, 0, 0, 0, 0, 1, 1, 2, 2, 2, 2, 3, 3, 3, 3, 3, 3, 2, 2, 2, 2, 1, 1, 1, 0, 0, 0, 0, 0, 0, 0, 0, 0, 0, 0, 0, 1, 1, 1, 2, 2, 3, 3, 4, 4, 5, 5, 6, 6, 7, 7, 8, 8, 8, 9, 9, 9, 9, 9, 9, 9, 9, 9, 9, 9, 9, 8, 8, 8, 7, 7, 7, 6, 6, 5, 5, 4, 4, 3, 3, 2, 2, 2, 1, 1, 1, 0, 0, 0, 0, 0, 0, 0, 0, 0, 0, 0, 0, 0, 1, 1, 1, 2, 2, 3, 3, 4, 4, 5,
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
};
inline void initFramePalettes(int remapVerticalOffset, const uint16_t *pCheckpointData)
{
	// This function must be called before the end of the vertical blank. It restores the palette modified by the inline color changing engine 
	uint8_t * pCurrentLevelColorToChangeIndex = (uint8_t*) ((customLevelData_t*)levels[currentLevel].customData)->colorToChangeIndex;
	uint8_t * pCurrentLevelNewColorTable = (uint8_t*)((customLevelData_t*)levels[currentLevel].customData)->newColorTable;
	uint8_t * pCurrentLevelRowPaletteIndexes = (uint8_t *) ((customLevelData_t*)levels[currentLevel].customData)->rowPaletteIndexes;
	int16_t * pCurrentLevelPaletteRowRemap	= (int16_t*) ((customLevelData_t*)levels[currentLevel].customData)->paletteRowRemap;
	// first we set the palette according to the checkpoint
	int checkpoint = (remapVerticalOffset >>  CHECKPOINT_PERIOD_LOG2);
	pCheckpointData += checkpoint * CHANGED_PALETTE_ENTRIES * CHECKPOINT_PALETTES;
	uint16_t *pPalette = ((uint16_t*) videoData.pPalette);
	for (int paletteN = 0; paletteN < CHECKPOINT_PALETTES; paletteN++)
	{
		for (int paletteEntry = 0; paletteEntry < CHANGED_PALETTE_ENTRIES; paletteEntry++)
		{
			uint16_t value = (*pCheckpointData++) & ~( 1 <<10);
			for (int i = 0; i < 16; i++)
			{
				pPalette[paletteEntry * 2 + 32 * i] = value;
				pPalette[paletteEntry * 32 + 2 * i + 1] = value;
			}
		}
		pPalette += 512;
	}
	// recalculate palettes in the remainder of the rows before actual line
	// for instance if the checkpoint period is 16, and we are at row 19, we have already performed checkpoint for line 16, but we need now to calculare lines 16, 17, 18 (19 will be done in the frame)
	int startRow = remapVerticalOffset & ~( ( 1 << CHECKPOINT_PERIOD_LOG2) - 1);
	// restore pPalette address
	for (int row = startRow; row < remapVerticalOffset; row++)
	{
		pPalette = ((uint16_t*) videoData.pPalette) + 512 * (pCurrentLevelRowPaletteIndexes[row] >> 4);
		uint16_t value = ((pCurrentLevelNewColorTable[row] * 1025) | 512) & ~(1 << 10);   // |512 is to set the correct gpio value. *1025 is to set the correct color signals.
		// NOTE: this works only when bytes are not packed.
		int paletteEntry = pCurrentLevelColorToChangeIndex[row];
		for (int i = 0; i < 16; i++)
		{
			pPalette[paletteEntry * 2 + 32 * i] = value;
			pPalette[paletteEntry * 32 + 2 * i + 1] = value;
		}
	}
	// put the correct pointers
	videoData.pNewColorChangeIndexTable = &pCurrentLevelColorToChangeIndex[remapVerticalOffset];
	videoData.pNewColorChangeTable = &pCurrentLevelNewColorTable[remapVerticalOffset];
	videoData.pPaletteIdx = &pCurrentLevelRowPaletteIndexes[remapVerticalOffset];
	videoData.pPaletteRemappingRowOffsets = &pCurrentLevelPaletteRowRemap[remapVerticalOffset * 2 + 16];  // the table allows a 8-pixel (offset 0..16) adjust of the water level
}
 int main(void) 
{	
	// NOTE! The videoData structure must be correctly initialized BEFORE Calling initUsvc!
	videoData.pPaletteIdx = (uint8_t*) level0_rowPaletteIndexes;
	videoData.pNewColorChangeTable = (uint8_t*) level0_newColorTable;
	videoData.pNewColorChangeIndexTable = (uint8_t*) level0_colorToChangeIndex;
	videoData.pPaletteRemappingRowOffsets = (int16_t*) level0_paletteRowRemap;
	// Only if you use row remapping videoData.ptrRowRemapTable = (uint8_t*) rowRemapTable; where rowRemapTable is 208-bytes (416 in hires mode) array (in flash or ram) of uint8_t.
	#if USE_ROW_REMAPPING
		videoData.ptrRowRemapTable = (uint8_t*) rowRemapTable;
	#endif
	// Only if you use per-line xScroll: videoData.ptrRowXScroll = xScrollTable; where xScrollTable is an array stored in flash o ram.
	#if PER_LINE_X_SCROLL
		videoData.ptrRowXScroll = xScrollTable;
	#endif
	#if PER_TILE_X_SCROLL
		videoData.ptrTileXScroll = xScrollTileTable;
		memset(xScrollTileTable, 0, sizeof(xScrollTileTable));
	#endif
	initUsvc(patches);
	uint32_t lastTime = millis();
	int testLed = 0;
	// KeyBuffer. It is 6-short long for keyboard support. Note that the keyboard/gamepad are ignored if SPRITE_IS_MOVED_BY_USB_INPUT is 0 
	uint16_t keyBuffer[6] = {0, 0, 0, 0, 0, 0};
	// used the same function created for REDBALLS. It copies and initializes all the data. 
	changeLevel(0);
	int16_t xScroll = 0;
	uint16_t lastHorseSound = 0;
	while (1)
	{
		uint32_t timeNow = millis();
		waitForVerticalBlank();
		soundEngine();			// called here to be sure it will be called at an almost constant position. 
		if (timeNow - lastTime > 1000UL)
		{
			setLed(testLed);
			testLed = 1 - testLed;
			lastTime = timeNow;
		}
		g_frame++;
		int8_t 	spriteFlags = 0;
		#if !SPRITE_IS_MOVED_BY_USB_INPUT
			keyBuffer[0] = 'd';
		#endif
		if (keyBuffer[0] == 'd')
		{
			xScroll+=2;
			if (xScroll >= currentLevelData.pixelSizeX - SCREEN_SIZE_X - 16)
				xScroll = 0;

		}
		else if (keyBuffer[0] == 'a')
		{
			spriteFlags = SPRITE_FLAGS_FLIP_HORIZONTAL;
			xScroll -= 2;
			if (xScroll < 0)
				xScroll = currentLevelData.pixelSizeX - SCREEN_SIZE_X - 16 - 2;
		}
		removeAllSprites(1);			// remove the sprites and redraw the screen (updating vram).
		// simple y position detector
		int y;
		int nextY;
		int currentXtile = (xScroll + 160) / TILE_SIZE_X;
		int nextXtile = ((xScroll + 160) / TILE_SIZE_X  + 1);
		if (nextXtile >= MAPSIZEX_LEVEL1 * 2)
			nextXtile = 0;
		if (g_frame - lastHorseSound > 4*57UL)
		{
			if (!(rand() & 31))
			{
				lastHorseSound = g_frame;
				triggerFx(5,255,FX_FLAGS_RETRIG | FX_FLAGS_SPECIFY_SAMPLE_FREQUENCY, 0x10000);
			}			
		}
		for (y = 15; y < MAPSIZEY_LEVEL1 * 2; y++)
		{			
			uint8_t type = tileProps[getMapTileFromTileCoordinatesWithMetaTiles( currentXtile, y) & 0x3FFF];
			if (type == TILEPROP_SOLID)
				break;
		}
		for (nextY = 15; nextY < MAPSIZEY_LEVEL1 * 2; nextY++)
		{
			uint8_t type = tileProps[getMapTileFromTileCoordinatesWithMetaTiles( nextXtile, nextY) & 0x3FFF];
			if (type == TILEPROP_SOLID)
				break;
		}
		
		// Smooth y change
		int yHorse = y * TILE_SIZE_Y  + (nextY - y) * (xScroll % TILE_SIZE_X) - 32;
		int yCamera = yHorse - 100;
		if (yCamera < 0 )
			yCamera = 0;
		if (yCamera > currentLevelData.pixelSizeY - 100)
			yCamera = currentLevelData.pixelSizeY - 100;
		// water mirror effect
		uint8_t f = g_frame % 57;
		for (int i = 0; i < sizeof(rowRemapTable) && i < 2 * (WATER_START - yCamera) ; i++)
		{
			rowRemapTable[i] = i / 2;
			xScrollTable[i] = 0;
		}
 		for (int i = 2 * (WATER_START - yCamera); i < sizeof(rowRemapTable) && i >= 0 ; i++)
 		{
			int index = (i - 2 * (WATER_START - yCamera));
 			rowRemapTable[i] = (WATER_START - yCamera) - index ;
			xScrollTable[i] = waterDisplacementArray[ f * MAX_WATER_INDEX + index];			
 		}
		// draw the map.	
		drawMap(xScroll, yCamera, 1);
		// put the horse sprite
    	putSprite(0, 160, yHorse - yCamera , SPRITE_FLAGS_HANDLE_CENTER | spriteFlags, (g_frame >> 2) & 7 );
		if ((g_frame & 31) == 16)
			triggerFx(4,255,FX_FLAGS_RETRIG | FX_FLAGS_SPECIFY_SAMPLE_FREQUENCY, 0x10000);
		// restore the palette to the correct values, based on the y offset
		initFramePalettes(yCamera, level0_checkpointData);
		// draw clouds
		int spriteNumber = 1;
		int xPatternPos =  (cloudPatternX   + (xScroll >> 2)) % CLOUD_PATTERN_WIDTH ;
		if (xPatternPos > 0)
			xPatternPos -= CLOUD_PATTERN_WIDTH;
		int yPatternPos = (yCamera >> 1);
		while (xPatternPos - xScroll < VRAMX * TILE_SIZE_X)
		{
			for (int i = 0; i < NUMBER_OF_CLOUDS; i++)
			{
				spriteNumber += putSprite(spriteNumber, xPatternPos + cloudX[i] - xScroll , cloudY[i] + yPatternPos - yCamera, SPRITE_FLAGS_PRIORITY_ALWAYS_BOTTOM | SPRITE_FLAGS_HANDLE_BOTTOMLEFT, cloudFrames[i]);
			}
			xPatternPos += CLOUD_PATTERN_WIDTH;
		}	
		// draw the sprites.
		drawSprites();
		// finally, redraw the fixed section
		#if USE_SECTION != NO_FIXED_SECTION
			drawFixedSection();
		#endif
		// now, we leave the remaining time for the USB
		do
		{
			#if !NO_USB
			usbHostTask();
			if (usbHidBootKeyboardIsInstalled())
			{
				usbKeyboardPoll();
				usbGetCurrentAsciiKeyboardStateEx(keyBuffer);
			}
			if (usbHidGenericGamepadIsInstalled())
			{
				gamePadState_t gps;
				usbHidGenericGamepadPoll();
				// gamepad to keyboard conversion
				getCurrentGamepadState(&gps);
				//
				keyBuffer[0] = 0;
				{
					uint8_t k = 0;
					if (gps.axes[1] == gps.XYZRxMinimum)
					{
						keyBuffer[k++] = 'w';
						if (gps.buttons == (GP_BUTTON_R1 | GP_BUTTON_L1 | GP_BUTTON_L2 | GP_BUTTON_R2))		// RESET
							keyBuffer[0] = USB_KEY_RESET;			
					}
				}		
			}
			if (keyBuffer[0] == USB_KEY_RESET)
			{  //  reset.
				SCB->AIRCR  = ((0x5FAUL << SCB_AIRCR_VECTKEY_Pos) |  SCB_AIRCR_SYSRESETREQ_Msk);
				while(1);
			}						
			#endif
		} while (getCurrentScanLineNumber() < VERTICAL_LINES_NUMBER - 2);
	}
}
