next-hack/uSVC/software/uSVC_Demos_And_Tutorials/uSVC_Demo-MovingSprites/demoMap.c

#include "demoMap.h"
const uint16_t demoMap[MAPSIZEY * MAPSIZEX] =
{
	0x0008, 0x0009, 0x000A, 0x000B, 0x0002, 0x0003, 0x0003, 0x0001,
	0x0002, 0x0003, 0x0001, 0x0008, 0x0009, 0x000A, 0x000B, 0x0002,
	0x0003, 0x0003, 0x0001, 0x0002, 0x0003, 0x0001, 0x0008, 0x0009,
	0x000A, 0x000B, 0x0002, 0x0003, 0x0003, 0x0001, 0x0002, 0x0003,
	0x0001, 0x0008, 0x0009, 0x000A, 0x000B, 0x0002, 0x0003, 0x0003,
	0x0001, 0x0002, 0x0003, 0x0001, 0x0008, 0x0009, 0x000A, 0x000B,
	0x0002, 0x0003, 0x0003, 0x0001, 0x0002, 0x0003, 0x0001, 0x0008,
	0x0009, 0x000A, 0x000B, 0x0002, 0x0003, 0x0003, 0x0001, 0x0002,
	0x0003, 0x0001, 0x0008, 0x0009, 0x000A, 0x000B, 0x0002, 0x0003,
	0x0003, 0x0001, 0x0002, 0x0003, 0x0001, 0x0008, 0x0009, 0x000A,
	0x000C, 0x000D, 0x000E, 0x000F, 0x0006, 0x0007, 0x0007, 0x0005,
	0x0006, 0x0007, 0x0005, 0x000C, 0x000D, 0x000E, 0x000F, 0x0006,
	0x0007, 0x0007, 0x0005, 0x0006, 0x0007, 0x0005, 0x000C, 0x000D,
	0x000E, 0x000F, 0x0006, 0x0007, 0x0007, 0x0005, 0x0006, 0x0007,
	0x0005, 0x000C, 0x000D, 0x000E, 0x000F, 0x0006, 0x0007, 0x0007,
	0x0005, 0x0006, 0x0007, 0x0005, 0x000C, 0x000D, 0x000E, 0x000F,
	0x0006, 0x0007, 0x0007, 0x0005, 0x0006, 0x0007, 0x0005, 0x000C,
	0x000D, 0x000E, 0x000F, 0x0006, 0x0007, 0x0007, 0x0005, 0x0006,
	0x0007, 0x0005, 0x000C, 0x000D, 0x000E, 0x000F, 0x0006, 0x0007,
	0x0007, 0x0005, 0x0006, 0x0007, 0x0005, 0x000C, 0x000D, 0x000E,
	0x0012, 0x0013, 0x0014, 0x0015, 0x0000, 0x0003, 0x0001, 0x0000,
	0x0001, 0x0010, 0x0011, 0x0012, 0x0013, 0x0014, 0x0015, 0x0000,
	0x0003, 0x0001, 0x0000, 0x0001, 0x0010, 0x0011, 0x0012, 0x0013,
	0x0014, 0x0015, 0x0000, 0x0003, 0x0001, 0x0000, 0x0001, 0x0010,
	0x0011, 0x0012, 0x0013, 0x0014, 0x0015, 0x0000, 0x0003, 0x0001,
	0x0000, 0x0001, 0x0010, 0x0011, 0x0012, 0x0013, 0x0014, 0x0015,
	0x0000, 0x0003, 0x0001, 0x0000, 0x0001, 0x0010, 0x0011, 0x0012,
	0x0013, 0x0014, 0x0015, 0x0000, 0x0003, 0x0001, 0x0000, 0x0001,
	0x0010, 0x0011, 0x0012, 0x0013, 0x0014, 0x0015, 0x0000, 0x0003,
	0x0001, 0x0000, 0x0001, 0x0010, 0x0011, 0x0012, 0x0013, 0x0014,
	0x0018, 0x0019, 0x001A, 0x001B, 0x0004, 0x0007, 0x0005, 0x0004,
	0x0005, 0x0016, 0x0017, 0x0018, 0x0019, 0x001A, 0x001B, 0x0004,
	0x0007, 0x0005, 0x0004, 0x0005, 0x0016, 0x0017, 0x0018, 0x0019,
	0x001A, 0x001B, 0x0004, 0x0007, 0x0005, 0x0004, 0x0005, 0x0016,
	0x0017, 0x0018, 0x0019, 0x001A, 0x001B, 0x0004, 0x0007, 0x0005,
	0x0004, 0x0005, 0x0016, 0x0017, 0x0018, 0x0019, 0x001A, 0x001B,
	0x0004, 0x0007, 0x0005, 0x0004, 0x0005, 0x0016, 0x0017, 0x0018,
	0x0019, 0x001A, 0x001B, 0x0004, 0x0007, 0x0005, 0x0004, 0x0005,
	0x0016, 0x0017, 0x0018, 0x0019, 0x001A, 0x001B, 0x0004, 0x0007,
	0x0005, 0x0004, 0x0005, 0x0016, 0x0017, 0x0018, 0x0019, 0x001A,
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
};
