next-hack/uSVC/software/uSVC_Demos_And_Tutorials/uSVC_Demo-MovingSprites/romTiles.c

/*
 * romTiles.c
 *
 * Created: 02/06/2020 10:48:04
 *  Author: PETN
 */ 
#include "romTiles.h"
const uint8_t tileData[MAXTILEINDEX][TILESIZEX * TILESIZEY ] =
{
	{
		0x4E, 0x4E, 0x4E, 0x4B,
		0x4B, 0x4A, 0x4A, 0x4D,
		0x4E, 0x4E, 0x4B, 0x4A,
		0x4A, 0x4D, 0x4D, 0x4C,
		0x4E, 0x4B, 0x4E, 0x4D,
		0x4D, 0x4D, 0x4D, 0x4C,
		0x4B, 0x4A, 0x4D, 0x4D,
		0x4D, 0x4D, 0x4C, 0x4C,
		0x4A, 0x4A, 0x4D, 0x4D,
		0x4D, 0x4D, 0x4C, 0x4C,
		0x4A, 0x4A, 0x4D, 0x4D,
		0x4C, 0x4C, 0x4C, 0x4C,
		0x4C, 0x4C, 0x4D, 0x4D,
		0x4C, 0x4C, 0x4C, 0x49,
		0x4C, 0x4C, 0x4C, 0x4C,
		0x4C, 0x4C, 0x49, 0x49
	},
	{
		0xDF, 0xDE, 0xDE, 0x9A,
		0x9D, 0x8C, 0x89, 0x58,
		0xDE, 0x9A, 0x9A, 0x9D,
		0x9D, 0x89, 0x89, 0x58,
		0xDE, 0x9A, 0x9D, 0x9D,
		0x89, 0x89, 0x88, 0x58,
		0x9A, 0x9D, 0x9D, 0x89,
		0x89, 0x89, 0x58, 0x58,
		0x9A, 0x9D, 0x9D, 0x89,
		0x89, 0x88, 0x58, 0x58,
		0x9A, 0x9D, 0x89, 0x89,
		0x89, 0x88, 0x58, 0x58,
		0x8C, 0x89, 0x89, 0x89,
		0x58, 0x58, 0x58, 0x58,
		0x88, 0x88, 0x58, 0x58,
		0x58, 0x58, 0x58, 0x49
	},
	{
		0x47, 0x47, 0x17, 0x17,
		0x16, 0x16, 0x16, 0x13,
		0x47, 0x17, 0x17, 0x17,
		0x17, 0x16, 0x13, 0x13,
		0x17, 0x17, 0x16, 0x16,
		0x16, 0x13, 0x13, 0x12,
		0x17, 0x17, 0x16, 0x16,
		0x13, 0x13, 0x13, 0x12,
		0x17, 0x17, 0x16, 0x16,
		0x13, 0x13, 0x13, 0x15,
		0x16, 0x16, 0x16, 0x13,
		0x13, 0x13, 0x13, 0x15,
		0x16, 0x16, 0x13, 0x13,
		0x13, 0x13, 0x12, 0x15,
		0x13, 0x13, 0x12, 0x12,
		0x15, 0x15, 0x15, 0x14
	},
	{
		0xE5, 0xE5, 0xE5, 0xE5,
		0xE5, 0xE5, 0xB5, 0x74,
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
		0x5C, 0x19, 0x19, 0x4C,
		0x48, 0x00, 0x00, 0x71,
		0x19, 0x5C, 0x19, 0x19,
		0x19, 0x19, 0x19, 0xA5,
		0x19, 0x71, 0x19, 0x5C,
		0x5C, 0x71, 0xA5, 0xA2,
		0x19, 0x75, 0x19, 0x19,
		0x19, 0x71, 0x71, 0x5C,
		0xA5, 0xA5, 0x19, 0x19,
		0x19, 0x19, 0x19, 0x19,
		0x75, 0x5C, 0x00, 0x00,
		0x00, 0x00, 0x19, 0x19,
		0x00, 0x00, 0x00, 0x00,
		0x00, 0x00, 0x00, 0x19
	},
	{
		0xA2, 0x19, 0x00, 0x00,
		0x00, 0x00, 0x00, 0x00,
		0xA2, 0x48, 0x00, 0x00,
		0x00, 0x00, 0x00, 0x00,
		0xB3, 0x00, 0x00, 0x00,
		0x00, 0x00, 0x00, 0x4C,
		0x71, 0x48, 0x00, 0x00,
		0x00, 0x4C, 0x19, 0x71,
		0x19, 0x19, 0x19, 0x19,
		0x71, 0x71, 0x75, 0xA5,
		0x19, 0x19, 0x5C, 0x71,
		0x75, 0x75, 0x75, 0x71,
		0x19, 0x19, 0x19, 0x19,
		0x19, 0x19, 0x19, 0x19,
		0x19, 0x19, 0x19, 0x4C,
		0x48, 0x00, 0x00, 0x4C
	},
	{
		0x4C, 0x19, 0x71, 0x71,
		0x75, 0x75, 0x19, 0x00,
		0x48, 0x5C, 0x5C, 0x19,
		0x19, 0x19, 0x19, 0x00,
		0x19, 0xA5, 0x71, 0x19,
		0x19, 0x19, 0x19, 0x19,
		0xA5, 0xB3, 0x71, 0x19,
		0x19, 0x4C, 0x4C, 0x19,
		0xA5, 0x75, 0x19, 0x4C,
		0x00, 0x00, 0x00, 0x00,
		0x19, 0x19, 0x48, 0x00,
		0x00, 0x00, 0x00, 0x00,
		0x19, 0x19, 0x00, 0x00,
		0x00, 0x00, 0x00, 0x00,
		0x19, 0x19, 0x00, 0x00,
		0x00, 0x00, 0x00, 0x00
	}
};
