next-hack/uSVC/software/uSVC_Demos_And_Tutorials/uSVC_Demo-MovingSprites16x16/romTiles.c

/*
 * romTiles.c
 *
 * Created: 02/06/2020 10:48:04
 *  Author: PETN
 */ 
#include "romTiles.h"
const uint8_t tileData[MAXTILEINDEX][TILESIZEX * TILESIZEY ] =
{
	{
		0xB3, 0xB3, 0xB3, 0xB3,
		0xB3, 0xB3, 0xB3, 0xB3,
		0xB3, 0xB3, 0xB3, 0xB3,
		0xB3, 0xB3, 0xB3, 0xB3,
		0xB3, 0xB3, 0xB3, 0xB3,
		0xB3, 0xB3, 0xB3, 0xB3,
		0xB3, 0xB3, 0xB3, 0xB3,
		0xB3, 0xB3, 0xB3, 0xB3,
		0xB3, 0xB3, 0xB3, 0xB3,
		0xB3, 0xB3, 0xB3, 0xB3,
		0xB3, 0xB3, 0xB3, 0xB3,
		0xB3, 0xB3, 0xB3, 0xB3,
		0xB3, 0xB3, 0xB3, 0xB3,
		0xB3, 0xB3, 0xB3, 0xB3,
		0xB3, 0xB3, 0xB3, 0xB3,
		0xB3, 0xB3, 0xB3, 0xB3
	},
	{
		0xB3, 0xB3, 0xB3, 0xB3,
		0xB3, 0xB3, 0xB3, 0xB3,
		0xB3, 0xB3, 0xB3, 0xB3,
		0xB3, 0xB3, 0xB3, 0xB3,
		0xB3, 0xB3, 0xB3, 0xB3,
		0xB3, 0xB3, 0xB3, 0xB3,
		0xB3, 0xB3, 0xB3, 0xB3,
		0xB3, 0xB3, 0xB3, 0xB3,
		0xB3, 0xB3, 0xB3, 0xB3,
		0xB3, 0xB3, 0xB3, 0xB3,
		0xB3, 0xB3, 0xB3, 0xB3,
		0xB3, 0xB3, 0xB3, 0xB3,
		0xB3, 0xB3, 0xB3, 0xB3,
		0x5A, 0x5A, 0x5A, 0x5A,
		0xB3, 0xB3, 0xB3, 0xB3,
		0x5A, 0x5A, 0x5A, 0x5A
	},
	{
		0xB3, 0xB3, 0xB3, 0xB3,
		0xB3, 0xB3, 0xB3, 0xB3,
		0xB3, 0xB3, 0xB3, 0xB3,
		0xB3, 0xB3, 0xB3, 0xB3,
		0xB3, 0xB3, 0xB3, 0xB3,
		0xB3, 0xB3, 0xB3, 0xB3,
		0xB3, 0xB3, 0xB3, 0xB3,
		0xB3, 0xB3, 0xB3, 0xB3,
		0xB3, 0xB3, 0xB3, 0xB3,
		0xB3, 0xB3, 0xB3, 0xB3,
		0xB3, 0xB3, 0xB3, 0xB3,
		0xB3, 0xB3, 0xB3, 0xB3,
		0x5A, 0x5A, 0x5A, 0x5A,
		0x5A, 0x5A, 0x5A, 0x5A,
		0x5A, 0x5A, 0x5A, 0x5A,
		0x5A, 0x5A, 0x5A, 0x5A
	},
	{
		0xB3, 0xB3, 0xB3, 0xB3,
		0xB3, 0xB3, 0xB3, 0xB3,
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
		0x11, 0x5D, 0x8B, 0x14,
		0x5A, 0x5A, 0xB3, 0x5D,
		0xA2, 0x14, 0x5D, 0x5A,
		0x5D, 0x01, 0x01, 0xB3,
		0xB3, 0x5D, 0x14, 0x14,
		0x5D, 0x5D, 0x5D, 0x5D,
		0x5A, 0x5A, 0x5D, 0x5A,
		0x5D, 0x5D, 0x5D, 0x5D,
		0x5A, 0x5A, 0x5A, 0x5A,
		0x5D, 0x5D, 0x5D, 0x5A,
		0x5A, 0x5A, 0x5A, 0x5A
	}
};
