next-hack/uSVC/software/uSVC_Demos_And_Tutorials/uSVC_RidingHorseDemo/VGAspriteData.c

/*
 *  Riding Horse demo. 
 *  Copyright 2019-2020 Nicola Wrachien (next-hack.com)
 *  A simple demo to show the most exciting features of the TILE_MODE22
 *  1) High res per line x scroll to create water deformation
 *  2) High res row remapping to create water mirror
 *  3) High res Palette change for water color distortion
 *  4) Per line color change to create sky shades
 *  5) Tile prioirity
 *  6) Sprite prioirity
 *
 *  Credits: the graphics of this game (namely the riding horse, the clouds and the tiles) have been taken from opengameart.org, and recoloured to better
 *  fit a 16-color palette.
 *  In particular:
 *  Original assassin character riding a horse: Author Stagnation. Original URL: https://opengameart.org/content/assassin-character-on-horse (License GPL3)
 *  Original classical ruin tiles: Author surt. Original URL: https://opengameart.org/content/classical-ruin-tiles (License: CC0 - public domain)
 *  The graphics is copyright of their respective authors. 
 *
 *  Note: this demo is not optimized for game, just to show some of the most important features all at once. 
 *  Better optimization (especially by using rom vectors) can be achieved fo save tons of RAM!
 *
 *  Warning: the code needs a clean-up, and there might be some unused additional files and functions.
 *
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
 *  tl;dr 
 *  Do whatever you want, this program is free! Though we won't 
 *  reject donations https://next-hack.com/index.php/donate/ :) 
 *
 */
#include "VGAspriteData.h"
#include "usvc_kernel/vga.h"
#include "stdint.h"
#if GFX_MODE == TILE_MODE1 || GFX_MODE == TILE_MODE2
const uint8_t spriteData[SPRITEDATA_NUMPIXELS] =
{
	0x00, 0x00, 0x00, 0x00, 0x00, 0x00, 0x00, 0x00, 0x00, 0x00, 0x00, 0x00, 0x00, 0x00, 0x00, 0x00,
	0x00, 0x00, 0x00, 0x00, 0x00, 0x00, 0x00, 0x00, 0x00, 0x90, 0xAA, 0x00, 0x00, 0x00, 0x00, 0x00,
	0x00, 0x00, 0x00, 0x00, 0x00, 0x00, 0x00, 0x00, 0x00, 0x00, 0x00, 0x00, 0x00, 0x00, 0x00, 0x00,
	0x00, 0x00, 0x00, 0x00, 0x00, 0x00, 0x00, 0x00, 0x00, 0x00, 0x00, 0x00, 0x00, 0x00, 0x00, 0x00,
	0x00, 0x00, 0x90, 0x99, 0xA9, 0x0A, 0x00, 0x00, 0x00, 0x00, 0x00, 0x00, 0x00, 0x00, 0x00, 0x00,
	0x00, 0x00, 0x00, 0x00, 0x00, 0x00, 0x00, 0x00, 0x00, 0x00, 0x00, 0x00, 0x00, 0x00, 0x00, 0x00,
	0x00, 0x00, 0x00, 0x00, 0x00, 0x00, 0x00, 0x00, 0x00, 0x00, 0x00, 0x00, 0x99, 0x99, 0xA9, 0x9A,
	0x00, 0x00, 0x00, 0x00, 0x00, 0x00, 0x00, 0x00, 0x00, 0x00, 0x00, 0x00, 0x00, 0x00, 0x00, 0x00,
	0x00, 0x00, 0x00, 0x00, 0x00, 0x00, 0x00, 0x00, 0x00, 0x00, 0x00, 0x00, 0x00, 0x00, 0x00, 0x00,
	0x00, 0x00, 0x00, 0x00, 0x00, 0x00, 0x99, 0x39, 0x99, 0x91, 0x00, 0x00, 0x00, 0x00, 0x00, 0x00,
	0x00, 0x00, 0x00, 0x00, 0x00, 0x00, 0x00, 0x00, 0x00, 0x00, 0x00, 0x00, 0x00, 0x00, 0x00, 0x00,
	0x00, 0x00, 0x00, 0x00, 0x00, 0x00, 0x00, 0x00, 0x00, 0x00, 0x00, 0x00, 0x00, 0x00, 0xAA, 0xAA,
	0x99, 0x93, 0x99, 0x91, 0x00, 0x00, 0x00, 0x00, 0x00, 0x00, 0x00, 0x00, 0x00, 0x00, 0x00, 0x00,
	0x00, 0x00, 0x00, 0x00, 0x00, 0x00, 0x00, 0x00, 0x00, 0x00, 0x00, 0x00, 0x00, 0x00, 0x00, 0x00,
	0x00, 0x00, 0x00, 0x00, 0x00, 0x00, 0x00, 0xAA, 0xAA, 0x9A, 0x33, 0x93, 0x99, 0x91, 0x00, 0x00,
	0x00, 0x00, 0x00, 0x00, 0x00, 0x00, 0x00, 0x00, 0x00, 0x00, 0x00, 0x00, 0x00, 0x00, 0x00, 0x00,
	0x00, 0x00, 0x00, 0x00, 0x00, 0x00, 0x00, 0x00, 0x00, 0x00, 0x00, 0x00, 0x00, 0x00, 0x00, 0x00,
	0xA0, 0x9A, 0x9A, 0xAA, 0x39, 0x99, 0x49, 0x91, 0x00, 0x00, 0x00, 0x00, 0x00, 0x00, 0x00, 0x50,
	0x00, 0x00, 0x00, 0x00, 0x00, 0x00, 0x00, 0x00, 0x00, 0x00, 0x00, 0x00, 0x00, 0x00, 0x00, 0x00,
	0x00, 0x00, 0x00, 0x00, 0x00, 0x00, 0x00, 0x00, 0x00, 0x00, 0xAA, 0x99, 0xAA, 0xAA, 0x9A, 0x99,
	0x19, 0x31, 0x00, 0x00, 0x00, 0x00, 0x00, 0x00, 0x00, 0x50, 0x05, 0x00, 0x00, 0x00, 0x00, 0x00,
	0x00, 0x00, 0x00, 0x00, 0x00, 0x00, 0x00, 0x00, 0x00, 0x00, 0x00, 0x00, 0x00, 0x00, 0x00, 0x00,
	0x00, 0x00, 0x00, 0x00, 0x9A, 0x99, 0xAA, 0xAA, 0x3A, 0x33, 0x11, 0x93, 0x09, 0x00, 0x00, 0x00,
	0x00, 0x11, 0x00, 0x50, 0x05, 0x00, 0x00, 0x00, 0x00, 0x00, 0x00, 0x00, 0x00, 0x00, 0x00, 0x00,
	0x00, 0x00, 0x00, 0x00, 0x00, 0x00, 0x00, 0x00, 0x00, 0x00, 0x00, 0x00, 0x00, 0xA0, 0x9A, 0xA3,
	0xAA, 0xAA, 0xAA, 0x9A, 0x39, 0x93, 0x09, 0x00, 0x00, 0x11, 0x11, 0x11, 0x11, 0x41, 0x55, 0x01,
	0x00, 0x00, 0x00, 0x00, 0x00, 0x00, 0x00, 0x00, 0x00, 0x00, 0x00, 0x00, 0x00, 0x00, 0x00, 0x00,
	0x00, 0x00, 0x00, 0x00, 0x00, 0x00, 0x00, 0x00, 0x39, 0x93, 0xAA, 0xAA, 0x3A, 0x13, 0x33, 0x93,
	0x99, 0x00, 0x00, 0x10, 0x11, 0x11, 0x11, 0x45, 0x55, 0x11, 0x00, 0x01, 0x00, 0x00, 0x00, 0x00,
	0x00, 0x00, 0x00, 0x00, 0x00, 0x00, 0x00, 0x00, 0x00, 0x00, 0x00, 0x00, 0x00, 0x00, 0x00, 0x00,
	0x00, 0x00, 0x11, 0x11, 0x99, 0xA9, 0x3A, 0x13, 0x33, 0x13, 0x99, 0x00, 0x00, 0x10, 0x11, 0x11,
	0x55, 0x66, 0x5B, 0x14, 0x11, 0x01, 0x00, 0x00, 0x00, 0x00, 0x00, 0x00, 0x00, 0x00, 0x00, 0x00,
	0x00, 0x00, 0x00, 0x00, 0x00, 0x00, 0x00, 0x00, 0x00, 0x00, 0x00, 0x10, 0x11, 0x11, 0x31, 0x99,
	0x19, 0x31, 0x33, 0x11, 0x91, 0x00, 0x00, 0x11, 0x11, 0x51, 0x66, 0x66, 0x4B, 0x55, 0x11, 0x00,
	0x00, 0x00, 0x00, 0x00, 0x00, 0x00, 0x00, 0x00, 0x00, 0x00, 0x00, 0x00, 0x00, 0x00, 0x00, 0x00,
	0x00, 0x00, 0x00, 0x00, 0x00, 0x22, 0x22, 0x11, 0x11, 0x31, 0x13, 0x11, 0x33, 0x11, 0x11, 0x10,
	0x11, 0x11, 0x11, 0x66, 0x66, 0x66, 0x68, 0x56, 0x05, 0x00, 0x00, 0x00, 0x00, 0x00, 0x00, 0x00,
	0x00, 0x00, 0x00, 0x00, 0x00, 0x00, 0x00, 0x00, 0x00, 0x00, 0x00, 0x00, 0x00, 0x00, 0x00, 0x22,
	0x22, 0x22, 0x12, 0x22, 0x11, 0x31, 0x00, 0x11, 0x11, 0x11, 0x11, 0x11, 0x61, 0x66, 0x66, 0x65,
	0x68, 0x33, 0x55, 0x00, 0x00, 0x00, 0x00, 0x00, 0x00, 0x00, 0x00, 0x00, 0x00, 0x00, 0x00, 0x00,
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
};
const frame_t frameData[FRAMEDATA_NUMFRAMES] =
{
	{ .w = 0x54,  .h = 0x34,  .ox = 0x2C,  .oy = 0x1E,  .pData = &spriteData[0x00000] },
	{ .w = 0x55,  .h = 0x34,  .ox = 0x2C,  .oy = 0x1E,  .pData = &spriteData[0x00888] },
	{ .w = 0x55,  .h = 0x3B,  .ox = 0x2C,  .oy = 0x1E,  .pData = &spriteData[0x01144] },
	{ .w = 0x56,  .h = 0x3B,  .ox = 0x2C,  .oy = 0x1E,  .pData = &spriteData[0x01B2D] },
	{ .w = 0x56,  .h = 0x3E,  .ox = 0x2B,  .oy = 0x1E,  .pData = &spriteData[0x02516] },
	{ .w = 0x57,  .h = 0x3E,  .ox = 0x2B,  .oy = 0x1E,  .pData = &spriteData[0x02F80] },
	{ .w = 0x58,  .h = 0x3D,  .ox = 0x2C,  .oy = 0x1D,  .pData = &spriteData[0x03A28] },
	{ .w = 0x59,  .h = 0x3D,  .ox = 0x2C,  .oy = 0x1D,  .pData = &spriteData[0x044A4] },
	{ .w = 0x5C,  .h = 0x3C,  .ox = 0x31,  .oy = 0x1C,  .pData = &spriteData[0x04F5D] },
	{ .w = 0x5D,  .h = 0x3C,  .ox = 0x31,  .oy = 0x1C,  .pData = &spriteData[0x05A25] },
	{ .w = 0x5D,  .h = 0x3C,  .ox = 0x31,  .oy = 0x1D,  .pData = &spriteData[0x06529] },
	{ .w = 0x5E,  .h = 0x3C,  .ox = 0x31,  .oy = 0x1D,  .pData = &spriteData[0x0702D] },
	{ .w = 0x56,  .h = 0x3E,  .ox = 0x2D,  .oy = 0x1E,  .pData = &spriteData[0x07B31] },
	{ .w = 0x57,  .h = 0x3E,  .ox = 0x2D,  .oy = 0x1E,  .pData = &spriteData[0x0859B] },
	{ .w = 0x57,  .h = 0x3D,  .ox = 0x2E,  .oy = 0x1E,  .pData = &spriteData[0x09043] },
	{ .w = 0x58,  .h = 0x3D,  .ox = 0x2E,  .oy = 0x1E,  .pData = &spriteData[0x09ABF] },
	{ .w = 0x50,  .h = 0x14,  .ox = 0x28,  .oy = 0x0A,  .pData = &spriteData[0x0A53B] },
	{ .w = 0x51,  .h = 0x14,  .ox = 0x28,  .oy = 0x0A,  .pData = &spriteData[0x0A85B] },
	{ .w = 0x40,  .h = 0x15,  .ox = 0x20,  .oy = 0x0A,  .pData = &spriteData[0x0AB8F] },
	{ .w = 0x41,  .h = 0x15,  .ox = 0x20,  .oy = 0x0A,  .pData = &spriteData[0x0AE2F] },
	{ .w = 0x50,  .h = 0x17,  .ox = 0x28,  .oy = 0x0B,  .pData = &spriteData[0x0B0E4] },
	{ .w = 0x51,  .h = 0x17,  .ox = 0x28,  .oy = 0x0B,  .pData = &spriteData[0x0B47C] },
	{ .w = 0x40,  .h = 0x27,  .ox = 0x20,  .oy = 0x13,  .pData = &spriteData[0x0B82B] },
	{ .w = 0x41,  .h = 0x27,  .ox = 0x20,  .oy = 0x13,  .pData = &spriteData[0x0BD0B] }
};
const anim_t animData[ANIMDATA_NUMANIM] =
{
	{ .frameIndex = 0x0000,  .numFrames = 0x08 },
	{ .frameIndex = 0x0008,  .numFrames = 0x01 },
	{ .frameIndex = 0x0009,  .numFrames = 0x01 },
	{ .frameIndex = 0x000A,  .numFrames = 0x01 },
	{ .frameIndex = 0x000B,  .numFrames = 0x01 }
};
const anim_t* entityData[ENTITYDATA_NUMENTITIES] =
{
	&animData[0x00],
	&animData[0x01],
	&animData[0x02],
	&animData[0x03],
	&animData[0x04]
};
const uint16_t entityAnimStartIndex[ENTITYDATA_NUMENTITIES] =
{
	0x00,
	0x01,
	0x02,
	0x03,
	0x04
};

#endif
