next-hack/uSVC/software/uSVC_Demos_And_Tutorials/uSVC_RidingHorseDemo/romTiles.c

/*
 *  Riding Horse demo. 
 *  Copyright 2019-2020 Nicola Wrachien (next-hack.com)
 *  A simple demo to show the most exciting features of the TILE_MODE22
 *  1) High res per line x scroll to create water deformation
 *  2) High res row remapping to create water mirror
 *  3) High res Palette change for water color distortion
 *  4) Per line color change to create sky shades
 *  5) Tile prioirity
 *  6) Sprite prioirity
 *
 *  Credits: the graphics of this game (namely the riding horse, the clouds and the tiles) have been taken from opengameart.org, and recoloured to better
 *  fit a 16-color palette.
 *  In particular:
 *  Original assassin character riding a horse: Author Stagnation. Original URL: https://opengameart.org/content/assassin-character-on-horse (License GPL3)
 *  Original classical ruin tiles: Author surt. Original URL: https://opengameart.org/content/classical-ruin-tiles (License: CC0 - public domain)
 *  The graphics is copyright of their respective authors. 
 *
 *  Note: this demo is not optimized for game, just to show some of the most important features all at once. 
 *  Better optimization (especially by using rom vectors) can be achieved fo save tons of RAM!
 *
 *  Warning: the code needs a clean-up, and there might be some unused additional files and functions.
 *
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
 *  tl;dr 
 *  Do whatever you want, this program is free! Though we won't 
 *  reject donations https://next-hack.com/index.php/donate/ :) 
 *
 */
#include "romTiles.h"
const uint8_t tileData[MAXTILEINDEX][TILESIZEX * TILESIZEY / 2 ] =
{
	{
		0xCC, 0xCC, 0xCC, 0xCC, 0xDD, 0xDD, 0xDD, 0xDD, 0xDD, 0xDD, 0xDD, 0xDD, 0x99, 0x99, 0x99, 0x99, 0xAA, 0xAA, 0xAA, 0xAA, 0x77, 0xA7, 0x77, 0x77, 0x77, 0xA7, 0x7C, 0x77, 0xAA, 0xAA, 0xA7, 0x7A
	},
	{
		0xCC, 0xCC, 0xCC, 0xCD, 0xDC, 0xDC, 0xCD, 0xDA, 0xDD, 0xDD, 0x9C, 0xDA, 0x99, 0x99, 0x99, 0x99, 0xAA, 0xAA, 0xAA, 0xAA, 0x77, 0x77, 0x7C, 0x77, 0x77, 0xA7, 0x77, 0x77, 0xA7, 0xAA, 0xA7, 0xAA
	},
	{
		0xCC, 0xCC, 0xCC, 0xCC, 0xDD, 0xDD, 0xDD, 0xCD, 0xDD, 0xDD, 0xDA, 0xDD, 0x99, 0x99, 0x99, 0x99, 0xAA, 0xAA, 0xAA, 0xAA, 0x77, 0xA7, 0x7C, 0x77, 0x77, 0xA7, 0x77, 0x77, 0xAA, 0x7A, 0xA7, 0xA7
	},
	{
		0xCC, 0xCC, 0xCC, 0xCC, 0xDD, 0xDD, 0xDD, 0xDD, 0xDD, 0xDD, 0xDD, 0xDD, 0x99, 0x99, 0x99, 0x99, 0xAA, 0xAA, 0xAA, 0xAA, 0x77, 0xA7, 0x7C, 0x77, 0x77, 0xA7, 0x77, 0x77, 0xAA, 0x7A, 0xA7, 0xAA
	},
	{
		0xCC, 0xCC, 0xCC, 0xCC, 0xDD, 0xDD, 0xDD, 0xDD, 0xDD, 0xDD, 0xDD, 0xDD, 0x99, 0x99, 0x99, 0x99, 0xAA, 0xAA, 0xAA, 0xAA, 0x77, 0xA7, 0x7C, 0x77, 0x77, 0xA7, 0x77, 0x77, 0xAA, 0x7A, 0xA7, 0xA7
	},
	{
		0xCC, 0xCC, 0xCC, 0xCD, 0xDC, 0xDC, 0xCD, 0xDA, 0xDD, 0xDD, 0x9C, 0xDA, 0x99, 0x99, 0x99, 0x99, 0xAA, 0xAA, 0xAA, 0xAA, 0x77, 0xA7, 0x7C, 0x77, 0x77, 0xA7, 0x77, 0x77, 0xAA, 0x7A, 0xA7, 0xAA
	},
	{
		0xCC, 0xCC, 0xCC, 0xAC, 0xDD, 0xDD, 0xCD, 0xAD, 0xDD, 0xAA, 0xDD, 0xAA, 0x99, 0x99, 0x99, 0x99, 0xAA, 0xA9, 0x9A, 0x00, 0x77, 0x77, 0x97, 0x00, 0x77, 0x77, 0x9A, 0x00, 0xA7, 0xA7, 0x99, 0x00
	},
	{
		0x00, 0x00, 0x00, 0x00, 0x00, 0x00, 0x00, 0x00, 0x00, 0x00, 0x00, 0x00, 0x00, 0x00, 0x00, 0x00, 0x00, 0x00, 0x00, 0x00, 0x00, 0x00, 0x00, 0x00, 0x00, 0x00, 0x00, 0x00, 0x00, 0x00, 0x00, 0x00
	},
	{
		0xCA, 0xCC, 0xCC, 0xCC, 0xDD, 0xDD, 0xDC, 0xDD, 0xDD, 0xAD, 0xDA, 0xDD, 0x99, 0x99, 0x99, 0x99, 0x00, 0x99, 0x99, 0xAA, 0x00, 0x77, 0xA7, 0x77, 0x00, 0x7C, 0x77, 0x77, 0x00, 0x99, 0xA9, 0x77
	},
	{
		0xCC, 0xCC, 0xCC, 0xCC, 0xDD, 0xDD, 0xDD, 0xDD, 0xDD, 0xDD, 0xDD, 0xDD, 0x99, 0x99, 0x99, 0x99, 0xAA, 0xAA, 0xAA, 0xAA, 0x77, 0x77, 0x77, 0xC7, 0x77, 0x77, 0x77, 0xC7, 0x77, 0x77, 0x77, 0x7A
	},
	{
		0xCC, 0xCC, 0xCC, 0xC9, 0xDD, 0xDD, 0x9D, 0xDC, 0xDD, 0xDD, 0x9A, 0xDD, 0x99, 0x99, 0x99, 0x9A, 0xAA, 0xAA, 0x9A, 0xAA, 0x77, 0x7A, 0x79, 0xC7, 0x77, 0x77, 0x7A, 0xC7, 0x77, 0x77, 0x7A, 0x9A
	},
	{
		0xCC, 0xC9, 0x9C, 0xCD, 0xAC, 0xD9, 0xC9, 0xDA, 0xAD, 0x99, 0x9C, 0xDA, 0x99, 0x99, 0x99, 0x99, 0x9A, 0xAA, 0xAA, 0xAA, 0x9A, 0x77, 0x7A, 0x77, 0xC9, 0x77, 0x77, 0x77, 0x7C, 0x77, 0x7A, 0x77
	},
	{
		0xCC, 0xCC, 0xCC, 0xCC, 0xDD, 0xDD, 0xDD, 0xDD, 0xDD, 0xDD, 0xDD, 0xDD, 0x99, 0x99, 0x99, 0x99, 0xAA, 0xAA, 0xAA, 0xAA, 0x77, 0x77, 0xC7, 0xC7, 0x77, 0x77, 0xC7, 0x77, 0x77, 0x77, 0x7A, 0x77
	},
	{
		0xCC, 0xCC, 0xCC, 0xCC, 0xDD, 0xDD, 0xDD, 0xDD, 0xDD, 0xDD, 0xDD, 0xDD, 0x99, 0x99, 0x99, 0x99, 0xAA, 0xA9, 0xAA, 0xAA, 0x77, 0x7A, 0x77, 0xA7, 0x77, 0x77, 0x77, 0x77, 0x77, 0x7A, 0x77, 0x77
	},
	{
		0xCC, 0xCC, 0xCC, 0xCC, 0xDD, 0xDD, 0xDD, 0xCD, 0xDD, 0xDD, 0xDA, 0xDD, 0x99, 0x99, 0x99, 0x99, 0xAA, 0xAA, 0x9A, 0xAA, 0x7C, 0x7C, 0xA7, 0x77, 0x7C, 0x77, 0x77, 0x77, 0x77, 0x77, 0xA7, 0x77
	},
	{
		0xCC, 0xCC, 0xCC, 0xCC, 0xDD, 0xDD, 0xDD, 0xDD, 0xDD, 0xDD, 0xDD, 0xDD, 0x99, 0x99, 0x99, 0x99, 0xAA, 0xAA, 0xAA, 0xAA, 0x77, 0xCA, 0x7C, 0x7C, 0x77, 0xC7, 0x77, 0x77, 0x77, 0x77, 0x77, 0x77
	},
	{
		0xCC, 0xCC, 0xCC, 0xCC, 0xDD, 0xDD, 0xDD, 0xDD, 0xDD, 0xDD, 0xDD, 0xDD, 0x99, 0x99, 0x99, 0x99, 0xAA, 0xAA, 0xAA, 0xAA, 0x77, 0xA7, 0x77, 0xC7, 0x77, 0x77, 0x77, 0xC7, 0x77, 0x77, 0xA7, 0x7A
	},
	{
		0xCC, 0xCC, 0xCC, 0xAC, 0xDC, 0xDD, 0xCD, 0xAD, 0xDD, 0xAA, 0xDD, 0xAA, 0x99, 0x99, 0x99, 0x99, 0xA9, 0xAA, 0x99, 0x00, 0x7A, 0xC7, 0xA7, 0x00, 0x7A, 0x77, 0x97, 0x00, 0xA7, 0xA9, 0x99, 0x00
	},
	{
		0xCA, 0xCC, 0xCC, 0xCC, 0xDD, 0xDD, 0xCC, 0xDD, 0xDD, 0xAD, 0xDA, 0xAD, 0x99, 0x99, 0x99, 0x99, 0x00, 0x99, 0x99, 0xAA, 0x00, 0x77, 0xA7, 0x77, 0x00, 0x77, 0x77, 0x77, 0x00, 0x99, 0xA9, 0x77
	},
	{
		0xCC, 0xCC, 0xCC, 0xCC, 0xDD, 0xDD, 0xDD, 0xCD, 0xDD, 0xDD, 0xDA, 0xDD, 0x99, 0x99, 0x99, 0x99, 0xAA, 0xAA, 0xAA, 0xAA, 0xA7, 0xCC, 0xC7, 0x77, 0x77, 0x7C, 0x77, 0x77, 0x77, 0x77, 0x77, 0x77
	},
	{
		0xCC, 0xCC, 0xCC, 0xCC, 0xDD, 0xDD, 0xDD, 0xDD, 0xDD, 0xDD, 0xDD, 0xDD, 0x99, 0x99, 0x99, 0x99, 0xAA, 0xAA, 0xAA, 0xAA, 0x77, 0x7A, 0x77, 0x77, 0x77, 0x77, 0x77, 0x77, 0x77, 0x77, 0x77, 0x77
	},
	{
		0xCC, 0xCC, 0xCC, 0xCC, 0xDD, 0xCD, 0xCD, 0xDD, 0xDD, 0xDD, 0xDD, 0xDD, 0x99, 0x99, 0x99, 0x99, 0xA9, 0xAA, 0xAA, 0xAA, 0x7A, 0x77, 0x77, 0x77, 0x7A, 0x77, 0x77, 0x7A, 0x77, 0x77, 0xCA, 0xCC
	},
	{
		0xCD, 0xCC, 0xCC, 0xCC, 0xCA, 0xDD, 0xDD, 0xDA, 0xDA, 0xDD, 0xDD, 0xDD, 0x99, 0x99, 0x99, 0x99, 0xAA, 0xAA, 0xA9, 0xAA, 0x77, 0x77, 0x77, 0x77, 0x77, 0x77, 0x77, 0xA7, 0xCC, 0xAC, 0x77, 0xA7
	},
	{
		0xCC, 0xCC, 0xCC, 0xCD, 0xDC, 0xDC, 0xCD, 0xDA, 0xDD, 0xDD, 0x9C, 0xDA, 0x99, 0x99, 0x99, 0x99, 0xAA, 0xAA, 0xA9, 0xAA, 0xC7, 0x77, 0x7A, 0x77, 0x77, 0x77, 0x77, 0x77, 0x77, 0x77, 0x7A, 0x77
	},
	{
		0xCC, 0xCC, 0xCC, 0xCC, 0xDD, 0xDD, 0xDD, 0xDD, 0xDD, 0xDD, 0xDD, 0xDD, 0x99, 0x99, 0x99, 0x99, 0xAA, 0xAA, 0xAA, 0xAA, 0x77, 0x7A, 0x77, 0x77, 0x77, 0x77, 0x77, 0x77, 0x77, 0x77, 0x7A, 0x9A
	},
	{
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
